nh-finescale/ln2block/documentation/img/Kranenburg.jpg

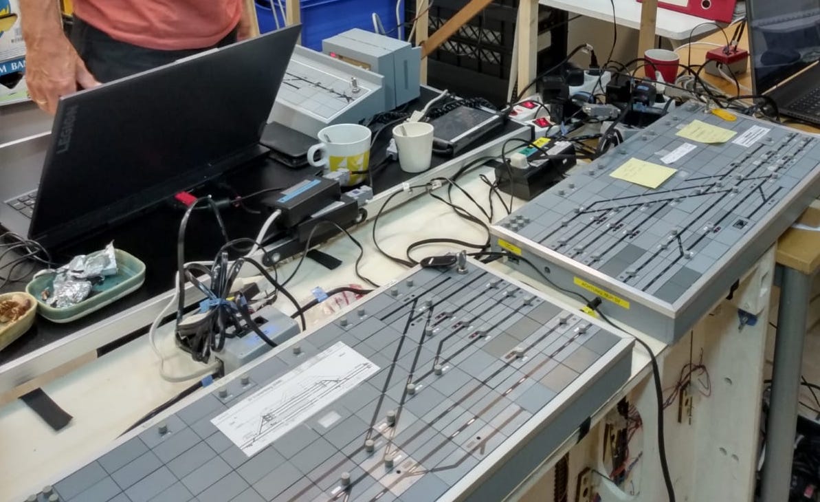
documentation/img/Kranenburg.jpg
