nh-finescale/ln2block/documentation/img/ln2b-statusdisplay.jpg

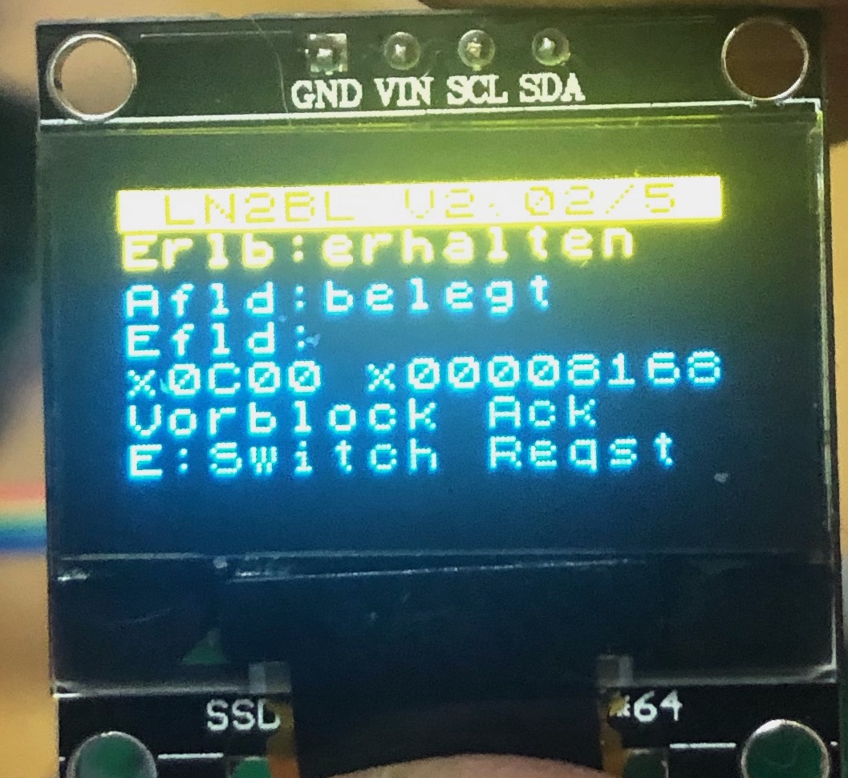
documentation/img/ln2b-statusdisplay.jpg
