nh-finescale/ln2block/documentation/img/ln2bv5-conn.png

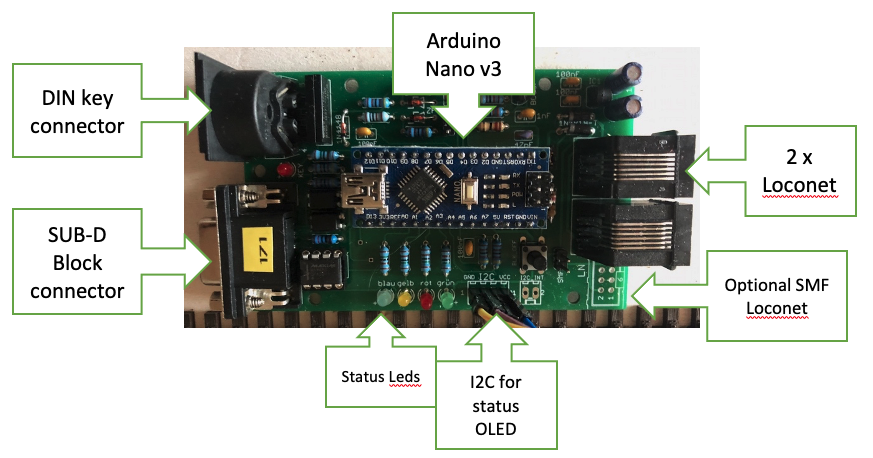
documentation/img/ln2bv5-conn.png
