nh-finescale/ln2block/documentation/img/ln2bv6s.jpg

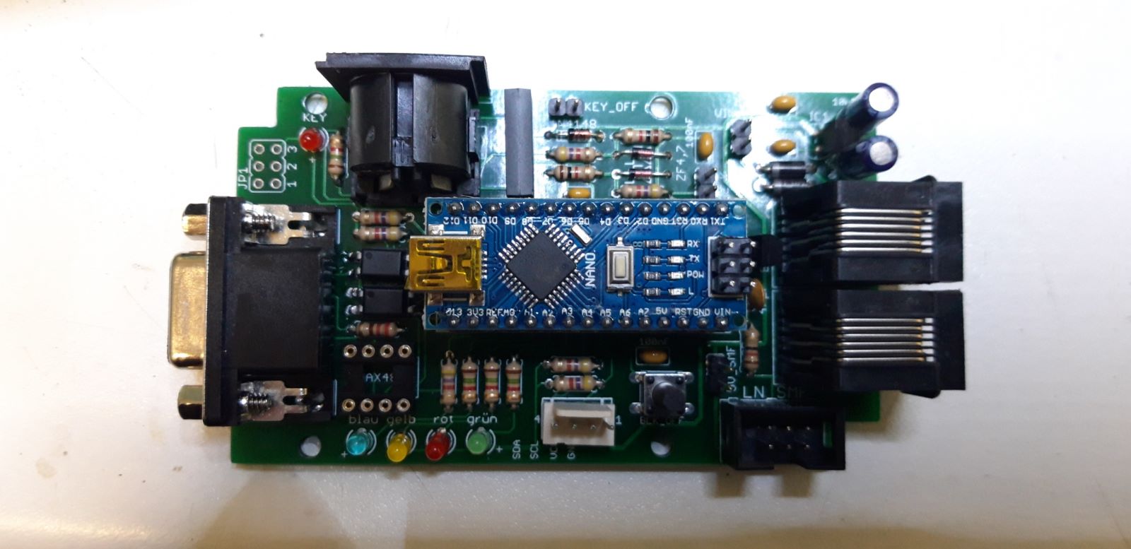
documentation/img/ln2bv6s.jpg
