nh-finescale/ln2block/documentation/img/LN2Block_Build_22.jpg

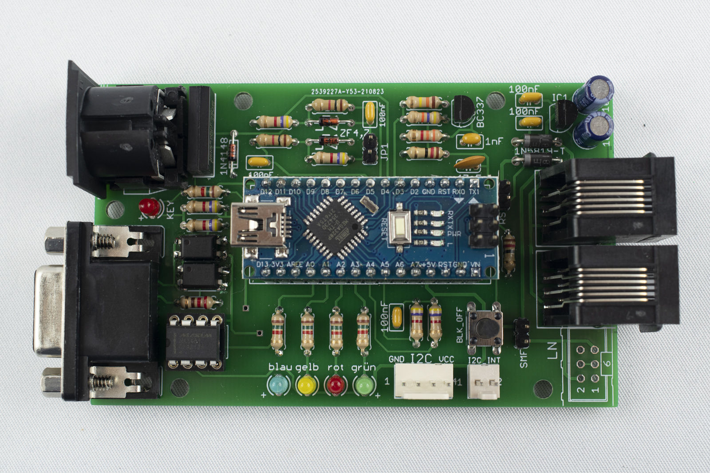
documentation/img/LN2Block_Build_22.jpg
