nh-finescale/ln2block/src/Loconet2Block/my_loconet.cpp

//##########################################################################
//#
//#		MyLoconetClass
//#
//#	Diese Klasse behandelt alle Loconet-Nachrichten und was damit
//#	zusammen hängt.
//#
//#-------------------------------------------------------------------------
//#
//#	File Version:	33		from: 30.05.2026
//#
//#	Implementation:
//#		-	add second track contact
//#			new function
//#				SendContactAusfahrtOccupied()
//#
//#-------------------------------------------------------------------------
//#
//#	File Version:	32		from: 01.01.2026
//#
//#	Implementation:
//#		-	add handling for a distant signal
//#			change in function
//#				LoconetReceived()
//#
//#-------------------------------------------------------------------------
//#
//#	File Version:	31		from: 21.08.2024
//#
//#	Implementation:
//#		-	improvement of notify messages
//#			don't react on notifySwitchReport and notifySwitchState
//#			to avoid missinterpretation of requests.
//#			delete functions
//#				notifySwitchReport()
//#				notifySwitchState()
//#
//#-------------------------------------------------------------------------
//#
//#	File version:	30		from: 12.11.2023
//#
//#	Implementation:
//#		-	switch to LocoNet Library V1.1.13
//#			change in function
//#				notifyLNCVread()
//#
//#-------------------------------------------------------------------------
//#
//#	File version:	29		from: 09.08.2023
//#
//#	Implementation:
//#		-	change handling of ESTGWJ mode
//#			new variable
//#				m_bIsEstwgjMode
//#			change in function
//#				Init()
//#				LoconetReceived()
//#
//#-------------------------------------------------------------------------
//#
//#	File version:	28		from: 07.08.2023
//#
//#	Bug Fix:
//#		-	problem after change of module address fixed
//#			change in function
//#				notifyLNCVwrite()
//#
//#-------------------------------------------------------------------------
//#
//#	File version:	27		from: 26.07.2023
//#
//#	Bug Fix:
//#		-	by mistake no acknowledge was send when receiving a programming
//#			start with broadcast as address.
//#
//#-------------------------------------------------------------------------
//#
//#	File version:	26		from: 18.07.2023
//#
//#	Bug Fix:
//#		-	do not go into prog mode when a programming start msg
//#			with broadcast address was detected
//#			change in function
//#				notifyLNCVprogrammingStart()
//#
//#-------------------------------------------------------------------------
//#
//#	File version:	25		from: 04.06.2023
//#
//#	Bug Fix:
//#		-	do not go into prog mode when a discover msg was detected
//#			change in function
//#				notifyLNCVdiscover()
//#
//#-------------------------------------------------------------------------
//#
//#	File version:	24		from: 16.05.2023
//#
//#	Implementation:
//#		-	new definitions for train number field types
//#				TRAIN_NUMBER_FIELD_ALL
//#			this type is used to address all ZN fields with one message
//#			changes in function
//#				CheckForMessageAndStoreInDataPool()
//#				SendBlock2Station()
//#
//#-------------------------------------------------------------------------
//#
//#	File version:	23		from: 07.04.2023
//#
//#	Bug Fix:
//#		-	ignore the second switch message with output set to '0'
//#			changes in functions
//#				LoconetReceived()
//#				notifySwitchRequest()
//#				notifySwitchReport()
//#				notifySwitchState()
//#
//#-------------------------------------------------------------------------
//#
//#	File version:	22		from: 07.02.2023
//#
//#	Bug Fix:
//#		-	wrong messages were send, so move the print out calls
//#			change in functions
//#				LoconetReceived()
//#				SendBlockMessage()
//#
//#-------------------------------------------------------------------------
//#
//#	File version:	21		from: 01.02.2023
//#
//#	Bug Fix:
//#		-	wrong message send by 'Rückblock'
//#
//#	Implementation:
//#		-	change train number field codes to new definitions
//#
//#-------------------------------------------------------------------------
//#
//#	File version:	20		from: 31.01.2023
//#
//#	Implementation:
//#		-	add ESTWGJ mode
//#			new function
//#				SendBlockMessage()
//#
//#-------------------------------------------------------------------------
//#
//#	File version:	19		from: 04.01.2023
//#
//#	Bug Fix:
//#		-	don't react on Loconet messages when Block is OFF
//#			new variable
//#				m_bBlockOn
//#
//#-------------------------------------------------------------------------
//#
//#	File version:	18		from: 15.12.2022
//#
//#	Bug Fix:
//#		-	handle the correct sturcture pointer to
//#			function getTrainNumber()
//#		-	forget to set usDigit in function DecodeTrainNumberDigit()
//#
//#-------------------------------------------------------------------------
//#
//#	File version:	17		from: 14.11.2022
//#
//#	Implementation:
//#		-	change loconet message handling
//#
//#-------------------------------------------------------------------------
//#
//#	File version:	16		from: 01.11.2022
//#
//#	Implementation:
//#		-	add message to switch the box OFF / ON
//#			changes in function 'LoconetReceived()'
//#
//#-------------------------------------------------------------------------
//#
//#	File version:	15		from: 02.10.2022
//#
//#	Implementation:
//#		-	add version number into EEPROM
//#			changes in function 'notifyLNCVwrite()'
//#		-	store article number and module address in global variables
//#			to simple access and speed up LNCV read and write
//#
//#-------------------------------------------------------------------------
//#
//#	File version:	14		from: 11.09.2022
//#
//#	Implementation:
//#		-	add new functions
//#				SendContactOccupied()	state of internal contact
//#				SendBlockOn()			state of block (ON / OFF)
//#		-	remove Function SendMessageWithInAdr() because it is
//#			not used anymore
//#
//#-------------------------------------------------------------------------
//#
//#	File version:	13		from: 09.09.2022
//#
//#	Implementation:
//#		-	the flag for train numbers moved to 'lncv_storage',
//#			because it will be stored permanent now.
//#
//#-------------------------------------------------------------------------
//#
//#	File version:	12		from: 28.08.2022
//#
//#	Implementation:
//#		-	add send the states of all OUT-Loconet-Devices
//#			changes in function
//#				LoconetReceived()
//#
//#-------------------------------------------------------------------------
//#
//#	File version:	11		from: 09.07.2022
//#
//#	Implementation:
//#		-	add reset functionality over loconet
//#			changes in functions
//#				CheckForMessageAndStoreInDataPool()
//#				LoconetReceived()
//#			add new variable m_bDoReset
//#
//#-------------------------------------------------------------------------
//#
//#	File version:	10		from: 04.03.2022
//#
//#	Bug Fix:
//#		-	correction of parameter usage for switching train number
//#			messages on / off
//#			 -	function LoconetReceived()
//#		-	avoid evaluation of per loop-back received train number message
//#			 -	new member variable 'm_bIgnoreMsg'
//#			 -	function Init()
//#			 -	function SendBlock2Station()
//#			 -	function CheckForMessageAndStoreInDataPool()
//#
//#-------------------------------------------------------------------------
//#
//#	File version:	9		from: 04.03.2022
//#
//#	Implementation:
//#		-	put indicator into ZN message which ZN field to address
//#		-	add flag that shows if handling of train number messages
//#			is enabled
//#
//#-------------------------------------------------------------------------
//#
//#	File version:	8		from: 26.02.2022
//#
//#	Implementation:
//#		-	add address for annunciator field use for train numbers
//#
//#-------------------------------------------------------------------------
//#
//#	File version:	7		from: 25.02.2022
//#
//#	Implementation:
//#		-	add new message handling for FREMO train numbers
//#
//#-------------------------------------------------------------------------
//#
//#	File version:	6		from: 15.01.2022
//#
//#	Bug Fix:
//#		-	In der Funktion 'notifyLNCVwrite()' wurde versehentlich der
//#			falsche Parameter an die Funktion 'PrintLncvReadWrite()'
//#			übergeben, so das der Text 'Read' ausgegeben wurde.
//#			Dies wurde korrigiert und es wird der Text 'Write' ausgegeben.
//#		-	In der Funktion 'notifyLNCVprogrammingStart()' wurde die
//#			Debugging-Ausgabe an das Ende der Funktion verschoben.
//#			Dadurch wird die Box-Adresse ausgegeben, wenn eine Broadcast-
//#			Nachricht benutzt wurde, um in den Programmiermodus zu wechseln.
//#
//#-------------------------------------------------------------------------
//#
//#	File version:	5		from: 29.12.2021
//#
//#	Implementation:
//#		-	Durch den Einbau von "Block On / Off" wurde die Initialisierung
//#			geändert. Dafür wurde die Funktion Init() angepasst,
//#			die Funktion StartLoconet2Block() gelöscht und die Funktion
//#			AskForSignalState() neu erstellt.
//#		-	Wenn der Programmiermodus beendet wird, wird nun ein RESET
//#			ausgelöst.
//#
//#-------------------------------------------------------------------------
//#
//#	File version:	4		from: 01.12.2021
//#
//#	Implementation:
//#		-	In der Funktion SendMessageWithInAdr() die Information
//#			nicht invertiert, wenn der interne Kontakt benutzt wird und
//#			es sich um eine Einfahr-Kontakt-Nachricht handelt.
//#
//#-------------------------------------------------------------------------
//#
//#	File version:	3		from: 12.11.2021
//#
//#	Implementation:
//#		-	Das Display kann nun um 180 Grad gedreht werden.
//#			Gesteuert wird dies durch das Konfigurationsbit 'DISPLAY_FLIP'.
//#			Ist das Bit gesetzt, wird das Display um 180 Grad gedreht.
//#			Funktion:	StartLoconet2Block()
//#
//#-------------------------------------------------------------------------
//#
//#	File version:	2		from: 28.10.2021
//#
//#	Implementation:
//#		-	Zwischen zwei zu sendenden Loconet-Nachrichten wird nun
//#			eine konfigurierbare Wartezeit gewartet.
//#			Funktionen:	SendMessageWithInAdr()
//#						SendMessageWithOutAdr()
//#
//#-------------------------------------------------------------------------
//#
//#	File version:	1		from: 14.09.2021
//#
//#	Implementation:
//#		-	first working version
//#
//##########################################################################


//==========================================================================
//
//		I N C L U D E S
//
//==========================================================================

#include "compile_options.h"

#include <Arduino.h>
#include <LocoNet.h>


#ifdef DEBUGGING_PRINTOUT
#include "debugging.h"
#endif

#include "my_loconet.h"
#include "data_pool.h"
#include "lncv_storage.h"
#include "signal_aspect_codes.h"



//==========================================================================
//
//		D E F I N I T I O N S
//
//==========================================================================

#if PLATINE_VERSION == 4
	#define LOCONET_TX_PIN			4
#else
	#define LOCONET_TX_PIN			7
#endif

#define	DIR_RED			0
#define DIR_THROWN		0
#define DIR_GREEN		1
#define DIR_CLOSED		1


//==========================================================================
//
//		G L O B A L   V A R I A B L E S
//
//==========================================================================

MyLoconetClass	 g_clMyLoconet		= MyLoconetClass();

LocoNetCVClass	 g_clLNCV;
lnMsg			*g_pLnPacket;

uint16_t	g_uiArticleNumber;
uint16_t	g_uiModuleAddress;


#ifdef DEBUGGING_PRINTOUT

char		g_chTrainNumber[] = "L 123456";


//==========================================================================
//
//		G L O B A L   F U N C T I O N S
//
//==========================================================================

//*****************************************************************
//	DecodeTrainNumberDigit
//
uint8_t DecodeTrainNumberDigit( uint8_t usValue )
{
	uint8_t		usDigit;
	bool		bFlash		= (0 != (0x10 & usValue));

	switch( usValue )
	{
		case ' ':
		case 'L':
		case 'B':
			usDigit = usValue;
			break;

		case 0x1E:
			bFlash = true;

		case 0x0E:
			usDigit = 'F';
			break;

		case 0x0F:
		case 0x1F:
			usDigit = ' ';
			break;

		default:
			bFlash   = (0 != (0x10 & usValue));
			usValue &= 0x0F;
			usDigit  = '0' + usValue;
			break;
	}
	
	if( bFlash )
	{
		usDigit |= 0x80;
	}
	
	return( usDigit );
}


//*****************************************************************
//	getTrainNumber
//
void getTrainNumber( uint8_t chDir, peerXferMsg *pMsg )
{
	g_chTrainNumber[ 0 ] = chDir;
	g_chTrainNumber[ 1 ] = ' ';
	g_chTrainNumber[ 2 ] = DecodeTrainNumberDigit( pMsg->d1 );
	g_chTrainNumber[ 3 ] = DecodeTrainNumberDigit( pMsg->d2 );
	g_chTrainNumber[ 4 ] = DecodeTrainNumberDigit( pMsg->d3 );
	g_chTrainNumber[ 5 ] = DecodeTrainNumberDigit( pMsg->d4 );
	g_chTrainNumber[ 6 ] = DecodeTrainNumberDigit( pMsg->d5 );
	g_chTrainNumber[ 7 ] = DecodeTrainNumberDigit( pMsg->d6 );
}

#endif


//==========================================================================
//
//		C L A S S   F U N C T I O N S
//
//==========================================================================


///////////////////////////////////////////////////////////////////////
//	CLASS: MyLoconetClass
//

//*****************************************************************
//	Constructor
//
MyLoconetClass::MyLoconetClass()
{
}


//*****************************************************************
//	Init
//
void MyLoconetClass::Init( void )
{
	m_bBlockOn			= true;
	m_bIgnoreMsg		= false;
	m_bDoReset			= false;

	g_uiArticleNumber	= g_clLncvStorage.ReadLNCV( LNCV_ADR_ARTIKEL_NUMMER );
	g_uiModuleAddress	= g_clLncvStorage.ReadLNCV( LNCV_ADR_MODULE_ADDRESS );

	m_bIsEstwgjMode		= g_clLncvStorage.IsConfigSet( ESTWGJ_MODE );

	LocoNet.init( LOCONET_TX_PIN );
}


//*****************************************************************
//	StartLoconet2Block
//
void MyLoconetClass::AskForSignalState( void )
{
	if( 0 < g_clLncvStorage.GetInAddress( IN_IDX_EINFAHR_SIGNAL ) )
	{
		LocoNet.reportSwitch( g_clLncvStorage.GetInAddress( IN_IDX_EINFAHR_SIGNAL ) );
	}

	if( 0 < g_clLncvStorage.GetInAddress( IN_IDX_AUSFAHR_SIGNAL ) )
	{
		LocoNet.reportSwitch( g_clLncvStorage.GetInAddress( IN_IDX_AUSFAHR_SIGNAL ) );
	}
}


//*****************************************************************
//	CheckForAndHandleMessage
//
bool MyLoconetClass::CheckForMessageAndStoreInDataPool( void )
{
	uint16_t	uiAddress = 0;
	

	g_pLnPacket = LocoNet.receive();

	while( g_pLnPacket )
	{
		if( m_bIgnoreMsg )
		{
			m_bIgnoreMsg = false;
		}
		else if( !LocoNet.processSwitchSensorMessage( g_pLnPacket ) )
		{
			if( !g_clLNCV.processLNCVMessage( g_pLnPacket ) )
			{
				if( 	(OPC_PEER_XFER == g_pLnPacket->px.command)
					&&	(16 == g_pLnPacket->px.mesg_size)			)
				{
					//----------------------------------------------
					//	this is a FREMO train number message
					//	so send it over the block cable
					//
					if(		g_clLncvStorage.IsTrainNumbersOn()
						&&	g_clLncvStorage.IsConfigSet( TRAIN_NUMBERS ) )
					{
						uiAddress  =  g_pLnPacket->px.dst_h << 7;
						uiAddress |= (g_pLnPacket->px.dst_l & 0x7F);

						g_pLnPacket->px.dst_h = 0;

						//------------------------------------------
						//	now tell the other end of the block
						//	cable which ZN field to address
						//
						if( 0x0000 == uiAddress )
						{
							g_pLnPacket->px.dst_l = TRAIN_NUMBER_FIELD_ALL;

							g_clDataPool.ReceiveTrainNoFromStation( (uint8_t *)g_pLnPacket );
#ifdef DEBUGGING_PRINTOUT
							getTrainNumber( 'L', (peerXferMsg *)g_pLnPacket );
							g_clDebugging.PrintTrainNumber( ZN_ALL, g_chTrainNumber );
#endif
						}
						else if( g_clLncvStorage.GetTrainNoAddressTrack() == uiAddress )
						{
							g_pLnPacket->px.dst_l = TRAIN_NUMBER_FIELD_TRACK;

							g_clDataPool.ReceiveTrainNoFromStation( (uint8_t *)g_pLnPacket );
#ifdef DEBUGGING_PRINTOUT
							getTrainNumber( 'L', (peerXferMsg *)g_pLnPacket );
							g_clDebugging.PrintTrainNumber( ZN_TRACK, g_chTrainNumber );
#endif
						}
						else if( g_clLncvStorage.GetTrainNoAddressOffer() == uiAddress )
						{
							g_pLnPacket->px.dst_l = TRAIN_NUMBER_FIELD_OFFER;

							g_clDataPool.ReceiveTrainNoFromStation( (uint8_t *)g_pLnPacket );
#ifdef DEBUGGING_PRINTOUT
							getTrainNumber( 'L', (peerXferMsg *)g_pLnPacket );
							g_clDebugging.PrintTrainNumber( ZN_OFFER, g_chTrainNumber );
#endif
						}
						else if( g_clLncvStorage.GetTrainNoAddressAnnunciatorRemote() == uiAddress )
						{
							g_pLnPacket->px.dst_l = TRAIN_NUMBER_FIELD_ANNUNCIATOR;

							g_clDataPool.ReceiveTrainNoFromStation( (uint8_t *)g_pLnPacket );
#ifdef DEBUGGING_PRINTOUT
							getTrainNumber( 'L', (peerXferMsg *)g_pLnPacket );
							g_clDebugging.PrintTrainNumber( ZN_ANNUNCIATOR, g_chTrainNumber );
#endif
						}
					}
				}
			}
		}

		if( m_bDoReset )
		{
			g_pLnPacket = NULL;
		}
		else
		{
			g_pLnPacket = LocoNet.receive();
		}
	}

	return( m_bDoReset );
}


//*****************************************************************
//	SendBlockMessage
//
void MyLoconetClass::SendBlockMessage(	uint16_t	uiAsSensor,
										uint16_t	uiIsInvert,
										bool		bIsSensor,
										uint8_t		usDir,
										uint8_t		usAdrIdx,
										uint8_t		usBlockMsg	)
{
	uint16_t	uiMask = 0x0001 << usAdrIdx;

	//--------------------------------------------------------
	//	first check if we are searching for a sensor message
	//	or a switch message.
	//
	//	bIsSensor == false	we are looking for switch messages
	//	bIsSensor == true	we are looking for sensor messages
	//
	//	uiAsSensor will hold the info if the message at the
	//	actual bit position (uiMask) is expected to be
	//	a sensor message or a switch message.
	//	(bit set => sensor message)
	//
	if( bIsSensor == (0 != (uiAsSensor & uiMask)) )
	{
		//------------------------------------------------
		//	Check if direction should be inverted
		//
		if( uiIsInvert & uiMask )
		{
			if( 0 == usDir )
			{
				usDir = 1;
			}
			else
			{
				usDir = 0;
			}
		}

		//------------------------------------------------
		//	only send the message when we get a 'GREEN'
		//	direction
		//
		if( 0 != usDir )
		{
			g_clDataPool.SetSendBlockMessage( 1 << usBlockMsg );

#ifdef DEBUGGING_PRINTOUT
			if( IN_IDX_BEDIENUNG_HILFSVORBLOCK == usAdrIdx )
			{
				g_clDebugging.PrintAnfangsfeldState( ANFANGSFELD_STATE_BELEGT );
			}
			else if( IN_IDX_BEDIENUNG_RUECKBLOCK == usAdrIdx )
			{
				g_clDebugging.PrintEndfeldState( ENDFELD_STATE_FREI );
			}
			else if( IN_IDX_BEDIENUNG_ERLAUBNISABGABE == usAdrIdx )
			{
				g_clDebugging.PrintErlaubnisState( ERLAUBNIS_STATE_ABGEGEBEN );
			}
#endif
		}
	}
}


//*****************************************************************
//	SendBlock2Station
//
void MyLoconetClass::SendBlock2Station( uint8_t *pMsg )
{
	lnMsg		*pHelper	= (lnMsg *)pMsg;
	uint16_t	 uiAddress	= 0;

	if( TRAIN_NUMBER_FIELD_ALL == pHelper->px.dst_l )
	{
		uiAddress = 0x0000;

#ifdef DEBUGGING_PRINTOUT
		getTrainNumber( 'B', (peerXferMsg *)pHelper );
		g_clDebugging.PrintTrainNumber( ZN_ALL, g_chTrainNumber );
#endif
	}
	else if( TRAIN_NUMBER_FIELD_ANNUNCIATOR == pHelper->px.dst_l )
	{
		uiAddress = g_clLncvStorage.GetTrainNoAddressAnnunciatorLocal();

#ifdef DEBUGGING_PRINTOUT
		getTrainNumber( 'B', (peerXferMsg *)pHelper );
		g_clDebugging.PrintTrainNumber( ZN_ANNUNCIATOR, g_chTrainNumber );
#endif
	}
	else if( TRAIN_NUMBER_FIELD_OFFER == pHelper->px.dst_l )
	{
		uiAddress = g_clLncvStorage.GetTrainNoAddressOffer();

#ifdef DEBUGGING_PRINTOUT
		getTrainNumber( 'B', (peerXferMsg *)pHelper );
		g_clDebugging.PrintTrainNumber( ZN_OFFER, g_chTrainNumber );
#endif
	}
	else if( TRAIN_NUMBER_FIELD_TRACK == pHelper->px.dst_l )
	{
		uiAddress = g_clLncvStorage.GetTrainNoAddressTrack();

#ifdef DEBUGGING_PRINTOUT
		getTrainNumber( 'B', (peerXferMsg *)pHelper );
		g_clDebugging.PrintTrainNumber( ZN_TRACK, g_chTrainNumber );
#endif
	}

	pHelper->px.dst_h = (uint8_t)((uiAddress >> 7) & 0x7F);
	pHelper->px.dst_l = (uint8_t)( uiAddress & 0x7F);

	//----------------------------------------------------------
	//	send out a train number message
	//	set flag to avoid evaluation of this msg by myself,
	//	because internal loop-back of loconet messages.
	//
	m_bIgnoreMsg = true;
	
	if( LN_DONE != LocoNet.send( pHelper ) )
	{
		m_bIgnoreMsg = false;
	}
}


//******************************************************************
//	SendContactOccupied
//------------------------------------------------------------------
//	This function sends a loconet message with the state of the
//	internal contact.
//	If the contact is occupied it sends a 'red' and
//	if the contact is free it sends a 'green'.
//
void MyLoconetClass::SendContactOccupied( bool bOccupied )
{
	uint16_t	config		= g_clLncvStorage.GetConfigReceive();
	uint16_t	inverted	= g_clLncvStorage.GetInvertReceive();
	uint16_t	adr			= g_clLncvStorage.GetInAddress( IN_IDX_EINFAHR_KONTAKT );
	uint8_t		dir			= DIR_GREEN;
	bool		bDoInvert	= false;
	bool		bIsSensor	= false;


	//---------------------------------------------------------
	//	send the message only if there is an address for it
	//
	if( 0 < adr )
	{
		if( bOccupied )
		{
			dir = DIR_RED;
		}

		//-----------------------------------------------------
		//	Check if 'dir' should be inverted
		//
		if( inverted & IN_MASK_EINFAHR_KONTAKT )
		{
			bDoInvert = true;
		}

		//-----------------------------------------------------
		//	Check if this should be a sensor
		//	or a switch message
		//
		if( config & IN_MASK_EINFAHR_KONTAKT )
		{
			bIsSensor = true;
		}

		SendMessage( adr, dir, bDoInvert, bIsSensor );
	}
}


#if PLATINE_VERSION == 7

//******************************************************************
//	SendContactAusfahrtOccupied
//------------------------------------------------------------------
//	This function sends a loconet message with the state of the
//	internal contact.
//	If the contact is occupied it sends a 'red' and
//	if the contact is free it sends a 'green'.
//
void MyLoconetClass::SendContactAusfahrtOccupied( bool bOccupied )
{
	uint16_t	config		= g_clLncvStorage.GetConfigReceive();
	uint16_t	inverted	= g_clLncvStorage.GetInvertReceive();
	uint16_t	mask		= (uint16_t)1;
	uint16_t	adr			= g_clLncvStorage.GetInAddress( IN_IDX_AUSFAHR_KONTAKT );
	uint8_t		dir			= DIR_GREEN;
	bool		bDoInvert	= false;
	bool		bIsSensor	= false;


	//---------------------------------------------------------
	//	send the message only if there is an address for it
	//
	if( 0 < adr )
	{
		if( bOccupied )
		{
			dir = DIR_RED;
		}

		//-----------------------------------------------------
		//	Check if 'dir' should be inverted
		//
		if( inverted & IN_MASK_AUSFAHR_KONTAKT )
		{
			bDoInvert = true;
		}

		//-----------------------------------------------------
		//	Check if this should be a sensor
		//	or a switch message
		//
		if( config & IN_MASK_AUSFAHR_KONTAKT )
		{
			bIsSensor = true;
		}

		SendMessage( adr, dir, bDoInvert, bIsSensor );
	}
}

#endif


//******************************************************************
//	SendBlockOn
//------------------------------------------------------------------
//	This function sends a loconet message with the state of the
//	block (ON / OFF)
//	If the block is ON it sends a 'green' and
//	if the block is OFF it sends a 'red'
//
void MyLoconetClass::SendBlockOn( bool bBlockOn )
{
	uint16_t	adr	= g_clLncvStorage.GetBlockOnOffAddress();
	uint8_t		dir	= DIR_RED;


	if( bBlockOn )
	{
		dir = DIR_GREEN;
	}

	//----	switch message  ---------------------------
	//
	LocoNet.requestSwitch( adr, 1, dir );

#ifdef DEBUGGING_PRINTOUT
	g_clDebugging.PrintReportSwitchMsg( adr, dir );
#endif

	//----	wait befor sending the next message  ------
	//
	delay( 10 + g_clLncvStorage.GetSendDelayTime() );

	LocoNet.requestSwitch( adr, 0, dir );


	//----	wait befor sending the next message  ---------------
	//
	delay( g_clLncvStorage.GetSendDelayTime() );
}


//******************************************************************
//	LoconetReceived
//------------------------------------------------------------------
//	This function checks if the received message is for 'us'.
//	This is done by checking whether the address of the message
//	matches one of the stored addresses.
//	If so, the corresponding bit of the 'InState' will be set
//	according to the info in the message.
//
void MyLoconetClass::LoconetReceived( bool isSensor, uint16_t adr, uint8_t dir )
{
	uint16_t	configRecv	= g_clLncvStorage.GetConfigReceive();
	uint16_t	inverted	= g_clLncvStorage.GetInvertReceive();
	uint16_t	mask		= 0x0001;


	//--------------------------------------------------------------
	//	Handle special messages like RESET
	//	the special messages must be of type 'switch'
	//
	if( !isSensor )
	{
		if( g_clLncvStorage.GetTrainNoAddressEnable() == adr )
		{
			//------------------------------------------------------
			//	this is the message to enable/disable handling of
			//	train number messages
			//
			if( DIR_RED == dir )
			{
				g_clLncvStorage.SetTrainNumbersOn( false );
			}
			else
			{
				g_clLncvStorage.SetTrainNumbersOn( true );
			}

			return;
		}

		//----------------------------------------------------------
		//	switch display between showing
		//		-	Loconet and block messages
		//		-	train numbers
		//
#ifdef DEBUGGING_PRINTOUT
		if( g_clLncvStorage.GetShowTrainNumbersAddress() == adr )
		{
			if( DIR_RED == dir )
			{
				g_clLncvStorage.SetShowTrainNumbers( false );
				g_clDebugging.PrintInfoLine( infoLineMessages );
			}
			else
			{
				g_clLncvStorage.SetShowTrainNumbers( true );
				g_clDebugging.PrintInfoLine( infoLineTrainNumbers );
			}
		}
#endif

		//----------------------------------------------------------
		//	send state for all OUT-Loconet-Devices
		//
		if( g_clLncvStorage.GetSendDeviceStateAddress() == adr )
		{
			g_clDataPool.SendOutState();

			return;
		}

		if( g_clLncvStorage.GetBlockOnOffAddress() == adr )
		{
			//------------------------------------------------------
			//	this is the message to switch the block on or off
			//
			if( DIR_RED == dir )
			{
				if( g_clLncvStorage.IsBlockOn() )
				{
					g_clLncvStorage.SetBlockOn( false );
					g_clDataPool.SwitchBlockOff();
					m_bBlockOn = false;
				}
			}
			else
			{
				g_clLncvStorage.SetBlockOn( true );
				m_bDoReset = true;
			}

			return;
		}

		if( g_clLncvStorage.GetResetAddress() == adr )
		{
			//------------------------------------------------------
			//	this is the message to do a reset of the box
			//
			m_bDoReset = true;

			return;
		}
	}

	//--------------------------------------------------------------
	//	if the block is switched OFF then stop processing here
	//
	if( !m_bBlockOn )
	{
		return;
	}

	//--------------------------------------------------------------
	//	ESTWGJ Mode
	//
	if( m_bIsEstwgjMode )
	{
		if( g_clLncvStorage.GetInAddress( IN_IDX_BEDIENUNG_RUECKBLOCK ) == adr )
		{
			SendBlockMessage(	configRecv, inverted, isSensor, dir,
								IN_IDX_BEDIENUNG_RUECKBLOCK,
								DP_BLOCK_MESSAGE_RUECKBLOCK			);
		}

		if( g_clLncvStorage.GetInAddress( IN_IDX_BEDIENUNG_HILFSVORBLOCK ) == adr )
		{
			SendBlockMessage(	configRecv, inverted, isSensor, dir,
								IN_IDX_BEDIENUNG_HILFSVORBLOCK,
								DP_BLOCK_MESSAGE_VORBLOCK			);
		}

		if( g_clLncvStorage.GetInAddress( IN_IDX_BEDIENUNG_ERLAUBNISABGABE ) == adr )
		{
			SendBlockMessage(	configRecv, inverted, isSensor, dir,
								IN_IDX_BEDIENUNG_ERLAUBNISABGABE,
								DP_BLOCK_MESSAGE_ERLAUBNIS_ABGABE	);
		}

		return;
	}

	//--------------------------------------------------------------
	//	block is ON, so process Loconet messages
	//
	for( uint8_t idx = 0 ; LOCONET_IN_COUNT > idx ; idx++ )
	{
		//--------------------------------------------------------
		//	first check if we are searching for an address in
		//	a sensor message or in a switch message.
		//
		//	isSensor == false	we are looking for switch messages
		//	isSensor == true	we are looking for sensor messages
		//
		//	configRecv will hold the info if the message at the
		//	actual bit position (mask) is expected to be
		//	a sensor message or a switch message.
		//	(bit set => sensor message)
		//
		if( isSensor == (0 != (configRecv & mask)) )
		{
			if(		(0 < g_clLncvStorage.GetInAddress( idx ))
				&&	(adr == g_clLncvStorage.GetInAddress( idx )) )
			{
				//------------------------------------------------
				//	This is one of our addresses, ergo go on
				//	with the processing...
				//

#ifdef DEBUGGING_PRINTOUT
				g_clDebugging.PrintNotifyMsg( idx, adr, dir, 0 );
#endif

				//------------------------------------------------
				//	Check if 'dir' should be inverted
				//
				if( inverted & mask )
				{
					if( 0 == dir )
					{
						dir = 1;
					}
					else
					{
						dir = 0;
					}
				}

				//------------------------------------------------
				//	always set the 'InState' if the message comes
				//	from a push button device.
				//	otherwise set the 'InState' according to
				//	the 'dir' parameter of the message
				//
//				if(		(0 != dir)
//					||	(	(IN_IDX_BEDIENUNG_RUECKBLOCK	 <= idx)
//						&&	(IN_IDX_BEDIENUNG_ANSCHALTER_AUS >= idx)) )
				if( 0 != dir )
				{
					g_clDataPool.SetInState( mask );
				}
				else
				{
					g_clDataPool.ClearInState( mask );
				}

				//------------------------------------------------
				//	store signal messages for 'Prüfschleife'
				//	and for an 'Einfahr-Signal' send the state
				//	over the block line to the next station
				//
				if( IN_IDX_EINFAHR_SIGNAL == idx )
				{
					g_clDataPool.SetInState( ((uint16_t)1 << DP_E_SIG_SEND) );

					if( 0 != dir )
					{
						g_clDataPool.SetDistantSignalAspect( SIGNAL_ASPECT_CODE__GO );
					}
					else
					{
						g_clDataPool.SetDistantSignalAspect( SIGNAL_ASPECT_CODE__STOP );
					}
				}
	
				if( IN_IDX_AUSFAHR_SIGNAL == idx )
				{
					g_clDataPool.SetInState( ((uint16_t)1 << DP_A_SIG_SEND) );
				}
			}
		}

		mask <<= 1;
	}
}


//*****************************************************************
//	SendMessage
//
void MyLoconetClass::SendMessage(	uint16_t	adr,
									uint8_t		dir,
									bool		bDoInvert,
									bool		bIsSensor	)
{
	//----------------------------------------------------------
	//	Check if 'dir' should be inverted
	//
	if( bDoInvert )
	{
		if( 0 < dir )
		{
			dir = 0;
		}
		else
		{
			dir = 1;
		}
	}

	//----------------------------------------------------------
	//	Check if this should be a sensor
	//	or a switch message
	//
	if( bIsSensor )
	{
		//----	sensor message  ----------------------------
		//
		LocoNet.reportSensor( adr, dir );

#ifdef DEBUGGING_PRINTOUT
		g_clDebugging.PrintReportSensorMsg( adr, dir );
#endif
	}
	else
	{
		//----	switch message  ----------------------------
		//
		LocoNet.requestSwitch( adr, 1, dir );

#ifdef DEBUGGING_PRINTOUT
		g_clDebugging.PrintReportSwitchMsg( adr, dir );
#endif

		//----	wait befor sending the next message  -------
		//
		delay( g_clLncvStorage.GetSendDelayTime() );

		LocoNet.requestSwitch( adr, 0, dir );
	}

	//----	wait befor sending the next message  -----------
	//
	delay( g_clLncvStorage.GetSendDelayTime() );
}


//*****************************************************************
//	SendMessageWithOutAdr
//
void MyLoconetClass::SendMessageWithOutAdr( uint8_t idx, uint8_t dir )
{
	uint32_t	configSend	= g_clLncvStorage.GetConfigSend();
	uint32_t	inverted	= g_clLncvStorage.GetInvertSend();
	uint32_t	mask		= (uint32_t)1;
	uint16_t	adr			= g_clLncvStorage.GetOutAddress( idx );
	bool		bDoInvert	= false;
	bool		bIsSensor	= false;

	//---------------------------------------------------------
	//	send the message only if there is an address for it
	//
	if( 0 < adr )
	{
		mask <<= idx;

		//-----------------------------------------------------
		//	Check if 'dir' should be inverted
		//
		if( inverted & mask )
		{
			bDoInvert = true;
		}

		//-----------------------------------------------------
		//	Check if this should be a sensor
		//	or a switch message
		//
		if( configSend & mask )
		{
			bIsSensor = true;
		}

		SendMessage( adr, dir, bDoInvert, bIsSensor );
	}
}


//==========================================================================
//
//		L O C O N E T   C A L L B A C K   F U N C T I O N S
//
//==========================================================================


//**********************************************************************
//
void notifySensor( uint16_t Address, uint8_t State )
{
#ifdef DEBUGGING_PRINTOUT
	g_clDebugging.PrintNotifyType( NT_Sensor );
#endif

	g_clMyLoconet.LoconetReceived( true, Address, State );
}


//**********************************************************************
//
void notifySwitchRequest( uint16_t Address, uint8_t Output, uint8_t Direction )
{
#ifdef DEBUGGING_PRINTOUT
	g_clDebugging.PrintNotifyType( NT_Request );
#endif

	if( Output )
	{
		g_clMyLoconet.LoconetReceived( false, Address, Direction );
	}
}



//**********************************************************************
//
int8_t notifyLNCVdiscover( uint16_t &ArtNr, uint16_t &ModuleAddress )
{
	ArtNr			 = g_uiArticleNumber;
	ModuleAddress	 = g_uiModuleAddress;

//	g_clDataPool.SetProgMode( true );

#ifdef DEBUGGING_PRINTOUT
	g_clDebugging.PrintLncvDiscoverStart( false, ArtNr, ModuleAddress  );
#endif

	return( LNCV_LACK_OK );
}


//**********************************************************************
//
int8_t notifyLNCVprogrammingStart( uint16_t &ArtNr, uint16_t &ModuleAddress )
{
	int8_t retval = -1;		//	default: ignore request
	
	if( g_uiArticleNumber == ArtNr )
	{
		if( 0xFFFF == ModuleAddress )
		{
			//-----------------------------------------------------
			//	valid article number, but broadcast address,
			//	so only give back Module Address
			//
//			g_clDataPool.SetProgMode( true );

			ModuleAddress	= g_uiModuleAddress;
			retval			= LNCV_LACK_OK;
		}
		else if( g_uiModuleAddress == ModuleAddress )
		{
			//-----------------------------------------------------
			//	valid article number and valid module address,
			//	so switch to programming mode
			//
			g_clDataPool.SetProgMode( true );

			retval	= LNCV_LACK_OK;
		}
	}

#ifdef DEBUGGING_PRINTOUT
	g_clDebugging.PrintLncvDiscoverStart( true, ArtNr, ModuleAddress  );
#endif

	return( retval );
}


//**********************************************************************
//
void notifyLNCVprogrammingStop( uint16_t ArtNr, uint16_t ModuleAddress )
{
#ifdef DEBUGGING_PRINTOUT
	g_clDebugging.PrintLncvStop();
#endif

	if( g_clDataPool.IsProgMode() )
	{
		if( 	(g_uiArticleNumber == ArtNr)
			&&	(g_uiModuleAddress == ModuleAddress) )
		{
			//------------------------------------------------------
			//	valid article number and valid module address,
			//	so switch off programming mode
			//
			g_clDataPool.SetProgMode( false );
		}
	}
}


//**********************************************************************
//
int8_t notifyLNCVread( uint16_t ArtNr, uint16_t Address, uint16_t &Value )
{
	int8_t retval = -1;		//	default: ignore request

	if( g_clDataPool.IsProgMode() && (g_uiArticleNumber == ArtNr) )
	{
		if( g_clLncvStorage.IsValidLNCVAddress( Address ) )
		{
			Value	= g_clLncvStorage.ReadLNCV( Address );
			retval	= LNCV_LACK_OK;
		}
		else
		{
			retval = LNCV_LACK_ERROR_UNSUPPORTED;
		}
	}

#ifdef DEBUGGING_PRINTOUT
	g_clDebugging.PrintLncvReadWrite( true, Address, Value );
#endif

	return( retval );
}


//**********************************************************************
//	notifyLNCVwrite
//----------------------------------------------------------------------
//	write the 'Value' into EEPROM, but only if the 'Address' is
//	NOT the article number address and NOT the version address
//
int8_t notifyLNCVwrite( uint16_t ArtNr, uint16_t Address, uint16_t Value )
{
	int8_t retval = -1;		//	default: ignore request

	if( g_clDataPool.IsProgMode() && (g_uiArticleNumber == ArtNr) )
	{
		if( g_clLncvStorage.IsValidLNCVAddress( Address ) )
		{
			if(		(LNCV_ADR_VERSION_NUMBER != Address)
				&&	(LNCV_ADR_ARTIKEL_NUMMER != Address) )
			{
				g_clLncvStorage.WriteLNCV( Address, Value );

				if( LNCV_ADR_MODULE_ADDRESS == Address )
				{
					g_uiModuleAddress = Value;
				}
			}

			retval = LNCV_LACK_OK;
		}
		else
		{
			retval = LNCV_LACK_ERROR_UNSUPPORTED;
		}
	}

#ifdef DEBUGGING_PRINTOUT
	g_clDebugging.PrintLncvReadWrite( false, Address, Value );
#endif

	return( retval );
}
