nh-finescale/ln2block/src/Loconet2Block/anfangsfeld.cpp

//##########################################################################
//#
//#		AnfangsfeldClass
//#
//#	This class contains the state machine for 'Anfangsfeld'
//#
//#-------------------------------------------------------------------------
//#
//#	File version:	11		from: 23.10.2025
//#
//#	Bug Fix:
//#		-	change control of LEDs from pin number to mask
//#
//#-------------------------------------------------------------------------
//#
//#	File version:	10		from: 02.08.2025
//#
//#	Implementation:
//#		-	add two LNCV addresses to differentiate between the sounds
//#			for Erlaubniswechsel, Vor- and Rueckblock
//#			change in function
//#				CheckState()
//#
//#-------------------------------------------------------------------------
//#
//#	File version:	9		from: 08.07.2025
//#
//#	Bug Fix:
//#		-	improvement of key box handling
//#			switch off of key permission whenever no "Ausfahrt" possible
//#			instead of only when "KEY_BOX_DIRECT" is configured
//#			change in function
//#				CheckState()
//#
//#-------------------------------------------------------------------------
//#
//#	File version:	8		from: 21.08.2024
//#
//#	Implementation:
//#		-	improvement of button handling
//#			reset of button states moved to 'Loconet2Block.ino'
//#			change in function
//#				CheckState()
//#
//#-------------------------------------------------------------------------
//#
//#	File version:	7		from: 16.01.2022
//#
//#	Bug Fix:
//#		-	Das 'Merken' von Tasten-Nachrichten führte immer wieder zu
//#			Problemen, wie z.B.: 'automatisches' Auslösen eines State-
//#			Wechsels. Dieses Problem ist nun behoben.
//#
//#-------------------------------------------------------------------------
//#
//#	File version:	6		from: 05.01.2022
//#
//#	Bug Fix:
//#		-	Die Ansteuerung des Anrückmelders war nicht in Ordnung.
//#			Sie funktioniert jetzt wie gewünscht.
//#
//#-------------------------------------------------------------------------
//#
//#	File version:	5		from: 29.12.2021
//#
//#	Implementation:
//#		-	Die Grüne LED zeigt nun den Zustand "Block belegt" an.
//#
//#-------------------------------------------------------------------------
//#
//#	File version:	4		from: 01.12.2021
//#
//#	Bug Fix:
//#		-	Im Zustand "ANFANGSFELD_STATE_FLUEGEL_KUPPLUNG" wird nun für
//#			den Felderblock die Auswertung der Nachrichten richtig
//#			verarbeitet.
//#
//#-------------------------------------------------------------------------
//#
//#	File version:	3		from: 15.11.2021
//#
//#	Implementation:
//#		-	Im Zustand "ANFANGSFELD_STATE_FLUEGEL_KUPPLUNG" wird nun,
//#			wenn das Konfig-Bit "FELDERBLOCK" gesetzt ist, kein
//#			automatischer Vorblock mehr gesendet.
//#			Stattdessen wird darauf gewartet, dass der Gleiskontakt wieder
//#			frei ist und dann "Hilfsvorblock" empfangen wurde.
//#
//#-------------------------------------------------------------------------
//#
//#	File version:	2		from: 13.10.2021
//#
//#	Bug Fix:
//#		-	Im Zustand "ANFANGSFELD_STATE_FAHRT" war die Abfrage für
//#			Einfahrkontakt oder Ausfahrkontakt fehlerhaft.
//#			Dies ist nun korrigiert.
//#
//#-------------------------------------------------------------------------
//#
//#	File version:	1		from: 14.09.2021
//#
//#	Implementation:
//#		-	first working version
//#
//##########################################################################


//==========================================================================
//
//		I N C L U D E S
//
//==========================================================================

#include "compile_options.h"

#include <Arduino.h>

#ifdef DEBUGGING_PRINTOUT
#include "debugging.h"
#endif

#include "anfangsfeld.h"
#include "data_pool.h"
#include "block_msg.h"
#include "io_control.h"


//==========================================================================
//
//		D E F I N I T I O N S
//
//==========================================================================


//==========================================================================
//
//		G L O B A L   V A R I A B L E S
//
//==========================================================================

AnfangsfeldClass	g_clAnfangsfeld		= AnfangsfeldClass();


//==========================================================================
//
//		C L A S S   F U N C T I O N S
//
//==========================================================================


///////////////////////////////////////////////////////////////////////
//	CLASS: AnfangsfeldClass
//

//*****************************************************************
//	Constructor
//-----------------------------------------------------------------
//	set the internal variables to their initial value
//	the initial state is 'ANFANGSFELD_STATE_FREI'.
//
//	IMPORTANT
//	'm_eOldState' must differ from 'm_eState' to perform
//	all actions for the initial state
//
AnfangsfeldClass::AnfangsfeldClass()
{
	m_eState				= ANFANGSFELD_STATE_FREI;
	m_eOldState				= ANFANGSFELD_STATE_FAHRT;
	m_ulAnfangsfeldMillis	= 0;
}

//*****************************************************************
//	CheckStates
//-----------------------------------------------------------------
//	This function is the heart of the state machine.
//	The data from the data pool and the current state are used
//	to check whether a state change should take place.
//-----------------------------------------------------------------
//	Principle of the state machine:
//	-	when entering a state (m_eOldState != m_eState)
//		actions are executed that are to be executed,
//		regardless of the previous state
//	-	in the state data from the data pool is checked
//		to find out whether a state change should take place.
//	-	if a state change should take place execute all actions
//		that are specific for this state change only.
//-----------------------------------------------------------------
//	RETURN-Wert
//		The actual or new state will be returned
//
anfangsfeld_state_t AnfangsfeldClass::CheckState( void )
{
	switch( m_eState )
	{
		//---------------------------------------------------------
		case ANFANGSFELD_STATE_FREI:
			if( m_eOldState != m_eState )
			{
				g_clDataPool.SetOutState(	OUT_MASK_FAHRT_MOEGLICH
										|	OUT_MASK_NICHT_ZWANGSHALT
										|	OUT_MASK_SCHLUESSELENTNAHME_MOEGLICH );
				g_clDataPool.ClearOutState(	OUT_MASK_AUSFAHRSPERRMELDER_TF71
										|	OUT_MASK_BLOCKMELDER_TF71
										|	OUT_MASK_VORBLOCKMELDER_RELAISBLOCK );

				g_clControl.LedOff( LED_GREEN );

#if PLATINE_VERSION > 3
				if( g_clLncvStorage.IsConfigSetAll( KEY_INTERFACE | KEY_BOX_DIRECT ) )
				{
					g_clControl.KeyRelaisOn();
					g_clControl.KeyLedOn();
				}
#endif

				m_eOldState = m_eState;

#ifdef DEBUGGING_PRINTOUT
				g_clDebugging.PrintAnfangsfeldState( ANFANGSFELD_STATE_FREI );
#endif
			}
			else if( g_clDataPool.IsOneInStateSet( IN_MASK_AUSFAHR_SIGNAL ) )
			{
				m_eState = ANFANGSFELD_STATE_FAHRT_PRE;
			}
			else if(	g_clDataPool.DarfHilfsvorblockSetzen()
					&&	g_clDataPool.IsOneInStateSet( IN_MASK_BEDIENUNG_HILFSVORBLOCK ) )
			{
				m_eState = ANFANGSFELD_STATE_BELEGT;
			}
			break;
			
		//---------------------------------------------------------
		case ANFANGSFELD_STATE_BELEGT:
			if( m_eOldState != m_eState )
			{
				g_clDataPool.SetSendBlockMessage( 1 << DP_BLOCK_MESSAGE_VORBLOCK );

				g_clDataPool.ClearOutState(	OUT_MASK_FAHRT_MOEGLICH
										|	OUT_MASK_NICHT_ZWANGSHALT
										|	OUT_MASK_SCHLUESSELENTNAHME_MOEGLICH
										|	OUT_MASK_WIEDERHOLSPERRMELDER_RELAISBLOCK );
				g_clDataPool.SetOutState(	OUT_MASK_BLOCKMELDER_TF71
										|	OUT_MASK_VORBLOCKMELDER_RELAISBLOCK );

				g_clControl.LedOn( LED_GREEN );

				if( g_clLncvStorage.IsConfigSet( KEY_INTERFACE ) )
				{
					g_clControl.KeyRelaisOff();
					g_clControl.KeyLedOff();
				}
				
				m_eOldState = m_eState;

#ifdef DEBUGGING_PRINTOUT
				g_clDebugging.PrintAnfangsfeldState( ANFANGSFELD_STATE_BELEGT );
#endif
			}
			else if( g_clDataPool.IsBlockMessageEmpfangen( 1 << DP_BLOCK_MESSAGE_RUECKBLOCK ) )
			{
				g_clDataPool.StartMelder( OUT_IDX_HUPE_RUECKBLOCK );

				m_eState = ANFANGSFELD_STATE_FREI;
			}
			break;
			
		//---------------------------------------------------------
		case ANFANGSFELD_STATE_FAHRT_PRE:
			if( m_eOldState != m_eState )
			{
				m_ulAnfangsfeldMillis	= millis() + cg_ulInterval_500_ms;	//	Timer starten
				m_eOldState				= m_eState;

				g_clDataPool.SetOutState(	OUT_MASK_AUSFAHRSPERRMELDER_TF71
										|	OUT_MASK_WIEDERHOLSPERRMELDER_RELAISBLOCK );
				g_clDataPool.ClearOutState(	OUT_MASK_SCHLUESSELENTNAHME_MOEGLICH );

				if( g_clLncvStorage.IsConfigSet( KEY_INTERFACE ) )
				{
					g_clControl.KeyRelaisOff();
					g_clControl.KeyLedOff();
				}

#ifdef DEBUGGING_PRINTOUT
				g_clDebugging.PrintAnfangsfeldState( ANFANGSFELD_STATE_FAHRT_PRE );
#endif
			}
			else if( millis() > m_ulAnfangsfeldMillis )
			{
				m_ulAnfangsfeldMillis = 0;

				g_clDataPool.ClearOutState( OUT_MASK_FAHRT_MOEGLICH );

				m_eState = ANFANGSFELD_STATE_FAHRT;
			}
			break;
			
		//---------------------------------------------------------
		case ANFANGSFELD_STATE_FAHRT:
			if( m_eOldState != m_eState )
			{
				m_eOldState = m_eState;

#ifdef DEBUGGING_PRINTOUT
				g_clDebugging.PrintAnfangsfeldState( ANFANGSFELD_STATE_FAHRT );
#endif
			}
			else if( g_clDataPool.IsOneInStateSet( IN_MASK_EINFAHR_SIGNAL ) )
			{
				m_eState = ANFANGSFELD_STATE_EINFAHR_SIGNAL;
			}
			else if( g_clDataPool.IsOneInStateSet(	IN_MASK_EINFAHR_KONTAKT
												|	IN_MASK_AUSFAHR_KONTAKT ) )
			{
				m_eState = ANFANGSFELD_STATE_FLUEGEL_KUPPLUNG;
			}
			else if( 	!g_clDataPool.IsOneInStateSet( IN_MASK_AUSFAHR_SIGNAL )
					&&	 g_clDataPool.IsOneInStateSet( IN_MASK_BEDIENUNG_HILFSVORBLOCK ) )
			{
				m_eState = ANFANGSFELD_STATE_BELEGT;
			}
			break;

		//---------------------------------------------------------
		case ANFANGSFELD_STATE_EINFAHR_SIGNAL:
			if( m_eOldState != m_eState )
			{
				m_eOldState = m_eState;

#ifdef DEBUGGING_PRINTOUT
				g_clDebugging.PrintAnfangsfeldState( ANFANGSFELD_STATE_EINFAHR_SIGNAL );
#endif
			}
			else if( !g_clDataPool.IsOneInStateSet( IN_MASK_EINFAHR_SIGNAL ) )
			{
				m_eState = ANFANGSFELD_STATE_FAHRT;
			}
			break;
			
		//---------------------------------------------------------
		case ANFANGSFELD_STATE_FLUEGEL_KUPPLUNG:
			if( m_eOldState != m_eState )
			{
				g_clDataPool.ClearOutState( OUT_MASK_NICHT_ZWANGSHALT );

				m_eOldState = m_eState;

#ifdef DEBUGGING_PRINTOUT
				g_clDebugging.PrintAnfangsfeldState( ANFANGSFELD_STATE_FLUEGEL_KUPPLUNG );
#endif
			}
			else if( !g_clDataPool.IsOneInStateSet( IN_MASK_AUSFAHR_SIGNAL ) )
			{
				//-------------------------------------------------
				//	Signal is back in Hp0
				//	check if a state change is required
				//
				if( g_clDataPool.IsOneOutStateSet( OUT_MASK_UEBERTRAGUNGSSTOERUNG ) )
				{
					m_eState = ANFANGSFELD_STATE_AUTO_VORBLOCK_GESTOERT;
				}
				else if( g_clLncvStorage.IsConfigSet( FELDERBLOCK ) )
				{
					//---------------------------------------------
					//	Felderblock
					//	no automatic VORBLOCK message
					//	wait for Hilfsvorblock message
					//
					if( g_clDataPool.IsOneInStateSet( IN_MASK_BEDIENUNG_HILFSVORBLOCK ) )
					{
						m_eState = ANFANGSFELD_STATE_BELEGT;
					}
				}
				else
				{
					//---------------------------------------------
					//	normal Block
					//	send automatic VORBLOCK message
					//
					m_eState = ANFANGSFELD_STATE_BELEGT;
				}
			}
			//-----------------------------------------------------
			//	Signal still NOT in Hp0
			//	so if someone pressed 'Hilfsvorblock' at this time
			//	then delete the flag to prevent an automatic
			//	VORBLOCK message when signal goes to Hp0
			//
			else if( g_clDataPool.IsOneInStateSet( IN_MASK_BEDIENUNG_HILFSVORBLOCK ) )
			{
				g_clDataPool.ClearInState( IN_MASK_BEDIENUNG_HILFSVORBLOCK );
			}
			break;
			
		//---------------------------------------------------------
		case ANFANGSFELD_STATE_AUTO_VORBLOCK_GESTOERT:
			if( m_eOldState != m_eState )
			{
				m_eOldState = m_eState;

#ifdef DEBUGGING_PRINTOUT
				g_clDebugging.PrintAnfangsfeldState( ANFANGSFELD_STATE_AUTO_VORBLOCK_GESTOERT );
#endif
			}
			else if( !g_clDataPool.IsOneOutStateSet( OUT_MASK_UEBERTRAGUNGSSTOERUNG ) )
			{
				if( g_clDataPool.IsOneInStateSet( IN_MASK_BEDIENUNG_HILFSVORBLOCK ) )
				{
					m_eState = ANFANGSFELD_STATE_BELEGT;
				}
			}
			break;
	}

	return( m_eState );
}
