nh-finescale/ln2block/src/Loconet2Block/debugging.cpp

//##########################################################################
//#
//#		DebuggingClass
//#
//#	Diese Klasse liefert Textausgaben an verschiedene Ausgabegeräte,
//#	z.B.: Serielle Schnittstelle oder OLED Display.
//#
//#-------------------------------------------------------------------------
//#
//#		OLED Display
//#
//#	the display can be switched between the following layouts:
//#		-	with Loconet and block messages
//#			 S                   1 1 1 1 1 1 1
//#			Z  0 1 2 3 4 5 6 7 8 9 0 1 2 3 4 5
//#			0    L N 2 B L   V x . m m . f f
//#			1  x H H H H   x H H H H H H H H
//#			2  E r l b : <Erlaubnis State>
//#			3  A f l d : <Anfangsfeld State>
//#			4  E f l d : <Endfeld State>
//#			5  S : 0 x 2 C     R : 0 x 9 0
//#			6  <Loconet messages>
//#			7  <Loconet message parameters>
//#
//#		-	with train numbers
//#			 S                   1 1 1 1 1 1 1
//#			Z  0 1 2 3 4 5 6 7 8 9 0 1 2 3 4 5
//#			0    L N 2 B L   V x . m m . f f
//#			1  x H H H H   x H H H H H H H H
//#			2  E r l b : <Erlaubnis State>
//#			3  A f l d : <Anfangsfeld State>
//#			4  E f l d : <Endfeld State>
//#			5  T r c k :   L   <ZN track>
//#			6  O f f r :   B   <ZN offer>
//#			7  A n n u :   L   <ZN annunciator>
//#
//#-------------------------------------------------------------------------
//#
//#	File version:	21		from: 28.04.2024
//#
//#	Bug Fix:
//#		-	parameters in function 'memcpy()' were swaped.
//#			change in function
//#				PrintTrainNumber()
//#
//#-------------------------------------------------------------------------
//#
//#	File version:	20		from: 12.11.2023
//#
//#	Implementation:
//#		-	switch to new OLED library => SimpleOled V1.2.1
//#			change in function
//#				Init()
//#
//#-------------------------------------------------------------------------
//#
//#	File version:	19		from: 10.08.2023
//#
//#	Implementation:
//#		-	add a check if a display is connected and if not don't send
//#			anything to the display
//#			new variable
//#				m_bDisplayPresent
//#			change in all functions
//#
//#-------------------------------------------------------------------------
//#
//#	File version:	18		from: 20.06.2023
//#
//#	Implementation:
//#		-	add functionality for the old style station interface
//#			new function
//#				PrintStationInterface()
//#
//#-------------------------------------------------------------------------
//#
//#	File version:	17		from: 16.05.2023
//#
//#	Implementation:
//#		-	new definition for function PrintTrainNumber()
//#				ZN_ALL	=>	clear all ZN fields
//#			changes in functions
//#				PrintTrainNumber()
//#
//#-------------------------------------------------------------------------
//#
//#	File version:	16		from: 06.03.2023
//#
//#	Bug Fix:
//#		-	wrong variable name when using the U8x8 library
//#			change in function
//#				PrintBlockOff()
//#		-	error when printing ZN numbers
//#			change in function
//#				PrintInfoLine()
//#				UpdateTrainNumber()
//#
//#-------------------------------------------------------------------------
//#
//#	File version:	15		from: 04.01.2023
//#
//#	Implementation:
//#		-	new order of display lines
//#		-	bitfield always visible
//#
//#-------------------------------------------------------------------------
//#
//#	File version:	14		from: 04.01.2023
//#
//#	Implementation:
//#		-	new Block Off printout
//#			new variable
//#				m_bBlockOn
//#
//#-------------------------------------------------------------------------
//#
//#	File version:	13		from: 15.12.2022
//#
//#	Bug Fix:
//#		-	train numbers were not shown on the display
//#			forget to check the flag m_bShowTrainNumbers in
//#			a lot of functions
//#
//#-------------------------------------------------------------------------
//#
//#	File version:	12		from: 09.12.2022
//#
//#	Implementation:
//#		-	streamlining debugging class
//#			remove function
//#				PrintText()
//#				PrintCounter()
//#				PrintMsgCount()
//#				PrintNotifySensorMsg()
//#
//#-------------------------------------------------------------------------
//#
//#	File version:	11		from: 24.11.2022
//#
//#	Implementation:
//#		-	only print information when data has changed
//#			changed function PrintDataPoolStatus()
//#		-	adjust all print texts to the same length
//#
//#-------------------------------------------------------------------------
//#
//#	File version:	10		from: 09.11.2022
//#
//#	Implementation:
//#		-	add usage of multiple devices with the same address
//#			changes in functions
//#				PrintNotifyType()
//#				PrintNotifyMsg()
//#
//#-------------------------------------------------------------------------
//#
//#	File version:	9		from: 02.10.2022
//#
//#	Implementation:
//#		-	change function 'PrintStorageCheck()' to print
//#				LNCV #0		module address
//#				LNCV #1		article number
//#
//#-------------------------------------------------------------------------
//#
//#	File version:	8		from: 26.08.2022
//#
//#	Implementation:
//#		-	support for U8x8lib added.
//#			new compiler switch 'USE_SIMPLE_LIB' in file compile_options.h
//#			if switch is set then the simple display library is used
//#			otherwise the U8x8lib is used.
//#
//#-------------------------------------------------------------------------
//#
//#	File version:	7		from: 05.03.2022
//#
//#	Implementation:
//#		-	change block message line to show the last send command
//#			and the last received command
//#		-	change function 'PrintSendBlockMsg()' to just have the
//#			command byte as parameter
//#
//#-------------------------------------------------------------------------
//#
//#	File version:	6		from: 26.02.2022
//#
//#	Implementation:
//#		-	change display library to simple_oled_sh1106 lib
//#
//#-------------------------------------------------------------------------
//#
//#	File version:	5		from: 26.02.2022
//#
//#	Implementation:
//#		-	Change version numbering
//#			the main version is now defined by the board version
//#			minor version is for new features
//#			bugfix is for changes in a feature
//#
//#-------------------------------------------------------------------------
//#
//#	File version:	4		from: 15.01.2022
//#
//#	Implementation:
//#		-	Es ist nun möglich, die Loconat-Nachrichten zu zählen und
//#			im Display anzeigen zu lassen.
//#			Gesteuert wird das ganz mit Hilfe von zwei Definitionen:
//#			-	#define COUNT_ALL_MESSAGES
//#			-	#define COUNT_MY_MESSAGES
//#			Wenn die Definition COUNT_ALL_MESSAGES aktiv ist, werden alle
//#			Nachrichten, die die Box erkennt gezählt und angezeigt.
//#			Wenn die Definition COUNT_MY_MESSAGES aktiv ist, werden nur
//#			die Nachrichten gezählt, die für die Box selber sind.
//#
//#-------------------------------------------------------------------------
//#
//#	File version:	3		from: 29.12.2021
//#
//#	Implementation:
//#		-	Eine neue Funktion hinzugefügt, die den "Block OFF" Zustand
//#			im Display anzeigt.
//#
//#-------------------------------------------------------------------------
//#
//#	File version:	2		from: 12.11.2021
//#
//#	Implementation:
//#		-	Das Display kann nun um 180 Grad gedreht werden.
//#			Dazu hat die Funktion "PrintTitle()" einen weitere Parameter
//#			'flipDisplay' bekommen, der die Drehung steuert.
//#			'0' =>	Display normal
//#			'1'	=>	Display gedreht
//#
//#-------------------------------------------------------------------------
//#
//#	File version:	1		from: 14.09.2021
//#
//#	Implementation:
//#		-	OLED Display
//#			The display has the following setup:
//#			 S                   1 1 1 1 1 1 1
//#			Z  0 1 2 3 4 5 6 7 8 9 0 1 2 3 4 5
//#			0    L N 2 B L   V x . m m . f f
//#			1  x H H H H   x H H H H H H H H
//#			2  E r l b : <Erlaubnis State>
//#			3  A f l d : <Anfangsfeld State>
//#			4  E f l d : <Endfeld State>
//#			5  S : 0 x 2 C     R : 0 x 9 0
//#			6  <Loconet messages>
//#			7  <Loconet message parameters>
//#
//##########################################################################


//==========================================================================
//
//		I N C L U D E S
//
//==========================================================================

#include "compile_options.h"


#ifdef DEBUGGING_PRINTOUT
//**************************************************************************
//**************************************************************************

#include <Arduino.h>
#include <avr/pgmspace.h>
#include <Wire.h>

#ifdef USE_SIMPLE_DISPLAY_LIB
	#include <SimpleOled.h>
#else
	#include <U8x8lib.h>
#endif

#include "debugging.h"
#include "block_msg.h"


//==========================================================================
//
//		D E F I N I T I O N S
//
//==========================================================================

#define BLINK_TIME					500


#define	DISPLAY_ADDRESS				60
#define SECOND_DISPLAY_ADDRESS		61

//----------------------------------------------------------------------
//	definition of display positions
//
#define BITFIELD_LINE				1
#define	BITFIELD_COLUMN				0
#define ERLAUBNIS_LINE				2
#define	ERLAUBNIS_COLUMN			5
#define	ANFANGSFELD_LINE			ERLAUBNIS_LINE + 1
#define	ANFANGSFELD_COLUMN			ERLAUBNIS_COLUMN
#define ENDFELD_LINE				ERLAUBNIS_LINE + 2
#define ENDFELD_COLUMN				ERLAUBNIS_COLUMN
#define BLOCK_MSG_LINE				5
#define BLOCK_MSG_SEND_COLUMN		0
#define BLOCK_MSG_RECEIVE_COLUMN	8
#define	LOCONET_MSG_LINE			6
#define LOCONET_MSG_COLUMN			0
#define INFO_LINE					7
#define INFO_COLUMN					0

#define ZN_TRACK_LINE				5
#define ZN_OFFER_LINE				6
#define ZN_ANNUNCIATOR_LINE			7
#define ZN_COLUMN					6

#define ZN_TEXT_LENGTH				8


//==========================================================================
//
//		G L O B A L   V A R I A B L E S
//
//==========================================================================

DebuggingClass	g_clDebugging	= DebuggingClass();

//----------------------------------------------------------------------
//	Variable für das OLED Display
//

#ifndef USE_SIMPLE_DISPLAY_LIB
U8X8_SH1106_128X64_NONAME_HW_I2C	u8x8( U8X8_PIN_NONE );
#endif

uint32_t	g_ulOldOutStatus	= 0x10000000L;
uint16_t	g_uiOldInStatus	= 0x1000;

char		g_chDebugString[ 18 ];
const char *g_chSwitch[] =
{
	"E_Sig     : ",
	"A_Sig     : ",
	"E_Kontakt : ",
	"A_Kontakt : ",
	"T_Rückblk : ",
	"T_H_Vorblk: ",
	"T_Erlbns  : ",
	"T_Ans_ON  : ",
	"T_Ans_OFF : ",
	"Key Free  : "
};

const char gc_strTrainNumberClear = { "        " };

uint8_t g_arTrainNumbers[ 3 ][ ZN_TEXT_LENGTH + 1 ] =
{
	"        ",
	"        ",
	"        "
};


//==========================================================================
//
//		C L A S S   F U N C T I O N S
//
//==========================================================================


////////////////////////////////////////////////////////////////////////
//	CLASS: DebuggingClass
//

//******************************************************************
//	Constructor
//
DebuggingClass::DebuggingClass()
{
	m_ulBlinkTime		= 0;
	m_bDisplayPresent	= false;
	m_bBlockOn			= true;
	m_bInvers			= true;
	m_bShowTrainNumbers	= false;
}


//******************************************************************
//	Init
//
void DebuggingClass::Init( void )
{
	uint8_t	usError;
	uint8_t	usAdr		= DISPLAY_ADDRESS;


	//------------------------------------------------------------------
	//	Check if Display can be connected under the given address
	//
	Wire.begin();
	Wire.beginTransmission( usAdr );
	usError = Wire.endTransmission();

	if( 0 == usError )
	{
		m_bDisplayPresent = true;
	}
	else
	{
		usAdr = SECOND_DISPLAY_ADDRESS;

		Wire.beginTransmission( usAdr );
		usError = Wire.endTransmission();

		if( 0 == usError )
		{
			m_bDisplayPresent = true;
		}
	}

	Wire.end();

	if( m_bDisplayPresent )
	{

#ifdef USE_SIMPLE_DISPLAY_LIB

		//g_clDisplay.Init( CHIP_TYPE_SSD1306, usAdr );
		g_clDisplay.Init( CHIP_TYPE_SH1106, usAdr );

#else

		u8x8.setI2CAddress( usAdr );
		u8x8.begin();
		u8x8.setFont( u8x8_font_chroma48medium8_r );

#endif

	}

	delay( 50 );
}


//******************************************************************
//	PrintTitle
//
void DebuggingClass::Loop( void )
{
	if( m_bDisplayPresent && m_bBlockOn && m_bShowTrainNumbers )
	{
		if( millis() > m_ulBlinkTime )
		{
			m_ulBlinkTime = millis() + BLINK_TIME;
			m_bInvers     = !m_bInvers;
			
			UpdateTrainNumber( ZN_TRACK );
			UpdateTrainNumber( ZN_OFFER );
			UpdateTrainNumber( ZN_ANNUNCIATOR );
		}
	}
}


//******************************************************************
//	PrintTitle
//
void DebuggingClass::PrintTitle(	uint8_t versionMain,
									uint8_t versionMinor,
									uint8_t versionBugFix,
									bool	flipDisplay		)
{
	if( m_bDisplayPresent )
	{

#ifdef USE_SIMPLE_DISPLAY_LIB

		g_clDisplay.Clear();
		g_clDisplay.Flip( flipDisplay );
		g_clDisplay.SetInverseFont( true );
		sprintf( g_chDebugString, " LN2BL V%d.%02d.%02d ",
				versionMain, versionMinor, versionBugFix );
		g_clDisplay.Print( g_chDebugString );
		g_clDisplay.SetInverseFont( false );

#else

		u8x8.clear();
		u8x8.setFlipMode( (flipDisplay ? 1 : 0) );
		u8x8.setInverseFont( 1 );
		sprintf( g_chDebugString, " LN2BL V%d.%02d.%02d ",
				versionMain, versionMinor, versionBugFix );
		u8x8.print( g_chDebugString );
		u8x8.setInverseFont( 0 );

#endif

	}
}


//******************************************************************
//	PrintInfoLine
//
void DebuggingClass::PrintStationInterface( bool bInterfaceConnected )
{
	if( m_bDisplayPresent )
	{

#ifdef USE_SIMPLE_DISPLAY_LIB

		g_clDisplay.Print( F( "  Intrfc: " ) );
		g_clDisplay.Print( (bInterfaceConnected ? "yes\n" : "no \n") );

#else

		u8x8.print( F( "  Intrfc: " ) );
		u8x8.print( (bInterfaceConnected ? "yes\n" : "no\n") );

#endif

	}
}


//******************************************************************
//	PrintInfoLine
//
void DebuggingClass::PrintInfoLine( info_lines_t number )
{
	if( m_bDisplayPresent )
	{

#ifdef USE_SIMPLE_DISPLAY_LIB

		switch( number )
		{
			case infoLineFields:
				g_clDisplay.SetCursor( ERLAUBNIS_LINE, 0 );
				g_clDisplay.Print( F( "Erlb:\nAfld:\nEfld:" ) );
				break;

			case infoLineInit:
				g_clDisplay.Print( F( "\n  Init:\n" ) );
				break;

			case infoLineLedTest:
				g_clDisplay.Print( F( "  LED Test\n" ) );
				break;

			case infoLineMessages:
				m_bShowTrainNumbers = false;

			case infoLineTrainNumbers:
				m_ulBlinkTime = 0L;
				g_clDisplay.ClearLine( ZN_TRACK_LINE );
				g_clDisplay.ClearLine( ZN_OFFER_LINE );
				g_clDisplay.ClearLine( ZN_ANNUNCIATOR_LINE );

				if( infoLineMessages == number )
				{
					break;
				}

				g_clDisplay.SetCursor( ZN_TRACK_LINE, 0 );
				g_clDisplay.Print( F( "Trck:\nOffr:\nAnnu:" ) );
				m_bShowTrainNumbers = true;
				m_bInvers			= true;
				break;

			default:
				break;
		}

#else

		switch( number )
		{
			case infoLineFields:
				u8x8.setCursor( 0, ERLAUBNIS_LINE );
				u8x8.print( F( "Erlb:\nAfld:\nEfld:" ) );
				break;

			case infoLineInit:
				u8x8.print( F( "\n  Init:\n" ) );
				break;

			case infoLineLedTest:
				u8x8.print( F( "  LED Test\n" ) );
				break;

			case infoLineMessages:
				m_bShowTrainNumbers = false;

			case infoLineTrainNumbers:
				m_ulBlinkTime = 0L;
				u8x8.clearLine( ZN_TRACK_LINE );
				u8x8.clearLine( ZN_OFFER_LINE );
				u8x8.clearLine( ZN_ANNUNCIATOR_LINE );

				if( infoLineMessages == number )
				{
					break;
				}

				u8x8.setCursor( 0, ZN_TRACK_LINE );
				u8x8.print( F( "Trck:\nOffr:\nAnnu:" ) );
				m_bShowTrainNumbers = true;
				m_bInvers			= true;
				break;

			default:
				break;
		}

#endif

	}
}


//******************************************************************
//	PrintBlockOff
//
void DebuggingClass::PrintBlockOff( void )
{
	m_bBlockOn = false;

	if( m_bDisplayPresent )
	{

#ifdef USE_SIMPLE_DISPLAY_LIB

		for( uint8_t idx = INFO_LINE ; ERLAUBNIS_LINE <= idx ; idx-- )
		{
			g_clDisplay.ClearLine( idx );
		}

		g_clDisplay.SetInverseFont( true );
		g_clDisplay.Print( F( "\n                \n  Block is OFF  \n                " ) );
		g_clDisplay.SetInverseFont( false );

#else

		for( uint8_t idx = INFO_LINE ; ERLAUBNIS_LINE <= idx ; idx-- )
		{
			u8x8.clearLine( idx );
		}

		u8x8.setCursor( INFO_COLUMN, ANFANGSFELD_LINE );
		u8x8.setInverseFont( 1 );
		u8x8.print( F( "                \n  Block is OFF  \n                " ) );
		u8x8.setInverseFont( 0 );

#endif

	}
}


//******************************************************************
//	PrintErlaubnisState
//
void DebuggingClass::PrintErlaubnisState( erlaubnis_state_t state )
{
	if( m_bDisplayPresent && m_bBlockOn )
	{

#ifdef USE_SIMPLE_DISPLAY_LIB

		g_clDisplay.SetCursor( ERLAUBNIS_LINE, ERLAUBNIS_COLUMN );

		switch( state )
		{
			case ERLAUBNIS_STATE_KEINER:
				g_clDisplay.Print( F( "keiner" ) );
				break;
				
			case ERLAUBNIS_STATE_ERHALTEN:
				g_clDisplay.Print( F( "erhalten " ) );
				break;
				
			case ERLAUBNIS_STATE_ABGEGEBEN_PRE:
				g_clDisplay.Print( F( "abgeg pre" ) );
				break;
				
			case ERLAUBNIS_STATE_ABGEGEBEN:
				g_clDisplay.Print( F( "abgegeben" ) );
				break;
		}

#else

		u8x8.setCursor( ERLAUBNIS_COLUMN, ERLAUBNIS_LINE );

		switch( state )
		{
			case ERLAUBNIS_STATE_KEINER:
				u8x8.print( F( "keiner" ) );
				break;
				
			case ERLAUBNIS_STATE_ERHALTEN:
				u8x8.print( F( "erhalten " ) );
				break;
				
			case ERLAUBNIS_STATE_ABGEGEBEN_PRE:
				u8x8.print( F( "abgeg pre" ) );
				break;
				
			case ERLAUBNIS_STATE_ABGEGEBEN:
				u8x8.print( F( "abgegeben" ) );
				break;
		}

#endif

	}
}


//******************************************************************
//	PrintAnfangsfeldState
//
void DebuggingClass::PrintAnfangsfeldState( anfangsfeld_state_t state )
{
	if( m_bDisplayPresent && m_bBlockOn )
	{

#ifdef USE_SIMPLE_DISPLAY_LIB

		g_clDisplay.SetCursor( ANFANGSFELD_LINE, ANFANGSFELD_COLUMN );

		switch( state )
		{
			case ANFANGSFELD_STATE_FREI:
				g_clDisplay.Print( F( "frei     " ) );
				break;

			case ANFANGSFELD_STATE_BELEGT:
				g_clDisplay.Print( F( "belegt   " ) );
				break;

			case ANFANGSFELD_STATE_FAHRT_PRE:
				g_clDisplay.Print( F( "fahrt pre" ) );
				break;

			case ANFANGSFELD_STATE_FAHRT:
				g_clDisplay.Print( F( "fahrt    " ) );
				break;

			case ANFANGSFELD_STATE_EINFAHR_SIGNAL:
				g_clDisplay.Print( F( "einfahrt " ) );
				break;

			case ANFANGSFELD_STATE_FLUEGEL_KUPPLUNG:
				g_clDisplay.Print( F( "fluegelkp" ) );
				break;

			case ANFANGSFELD_STATE_AUTO_VORBLOCK_GESTOERT:
				g_clDisplay.Print( F( "auto err " ) );
				break;
		}

#else

		u8x8.setCursor( ANFANGSFELD_COLUMN, ANFANGSFELD_LINE );

		switch( state )
		{
			case ANFANGSFELD_STATE_FREI:
				u8x8.print( F( "frei     " ) );
				break;

			case ANFANGSFELD_STATE_BELEGT:
				u8x8.print( F( "belegt   " ) );
				break;

			case ANFANGSFELD_STATE_FAHRT_PRE:
				u8x8.print( F( "fahrt pre" ) );
				break;

			case ANFANGSFELD_STATE_FAHRT:
				u8x8.print( F( "fahrt    " ) );
				break;

			case ANFANGSFELD_STATE_EINFAHR_SIGNAL:
				u8x8.print( F( "einfahrt " ) );
				break;

			case ANFANGSFELD_STATE_FLUEGEL_KUPPLUNG:
				u8x8.print( F( "fluegelkp" ) );
				break;

			case ANFANGSFELD_STATE_AUTO_VORBLOCK_GESTOERT:
				u8x8.print( F( "auto err " ) );
				break;
		}

#endif

	}
}


//******************************************************************
//	PrintEndfeldState
//
void DebuggingClass::PrintEndfeldState( endfeld_state_t state )
{
	if( m_bDisplayPresent && m_bBlockOn )
	{

#ifdef USE_SIMPLE_DISPLAY_LIB

		g_clDisplay.SetCursor( ENDFELD_LINE, ENDFELD_COLUMN );

		switch( state )
		{
			case ENDFELD_STATE_FREI_BOOT:
				g_clDisplay.Print( F( "frei boot" ) );
				break;

			case ENDFELD_STATE_FREI:
				g_clDisplay.Print( F( "frei     " ) );
				break;

			case ENDFELD_STATE_BELEGT:
				g_clDisplay.Print( F( "belegt   " ) );
				break;

			case ENDFELD_STATE_SIGNAL_GEZOGEN:
				g_clDisplay.Print( F( "signal   " ) );
				break;

			case ENDFELD_STATE_ANSCHALTER_AKTIV:
				g_clDisplay.Print( F( "anschalt " ) );
				break;

			case ENDFELD_STATE_ERSTE_ACHSE:
				g_clDisplay.Print( F( "1. achse " ) );
				break;

			case ENDFELD_STATE_GERAEUMT:
				g_clDisplay.Print( F( "geraeumt " ) );
				break;
		}

#else

		u8x8.setCursor( ENDFELD_COLUMN, ENDFELD_LINE );

		switch( state )
		{
			case ENDFELD_STATE_FREI_BOOT:
				u8x8.print( F( "frei boot" ) );
				break;

			case ENDFELD_STATE_FREI:
				u8x8.print( F( "frei     " ) );
				break;

			case ENDFELD_STATE_BELEGT:
				u8x8.print( F( "belegt   " ) );
				break;

			case ENDFELD_STATE_SIGNAL_GEZOGEN:
				u8x8.print( F( "signal   " ) );
				break;

			case ENDFELD_STATE_ANSCHALTER_AKTIV:
				u8x8.print( F( "anschalt " ) );
				break;

			case ENDFELD_STATE_ERSTE_ACHSE:
				u8x8.print( F( "1. achse " ) );
				break;

			case ENDFELD_STATE_GERAEUMT:
				u8x8.print( F( "geraeumt " ) );
				break;
		}

#endif

	}
}


//******************************************************************
//	PrintSendBlockMsg
//
void DebuggingClass::PrintSendBlockMsg( uint8_t msg )
{
	if( m_bDisplayPresent && m_bBlockOn && !m_bShowTrainNumbers )
	{

#ifdef USE_SIMPLE_DISPLAY_LIB

		g_clDisplay.SetCursor( BLOCK_MSG_LINE, BLOCK_MSG_SEND_COLUMN );
		sprintf( g_chDebugString, "S:0x%02X", msg );
		g_clDisplay.Print( g_chDebugString );

#else

		u8x8.setCursor( BLOCK_MSG_SEND_COLUMN, BLOCK_MSG_LINE );
		sprintf( g_chDebugString, "S:0x%02X", msg );
		u8x8.print( g_chDebugString );

#endif

	}
}


//******************************************************************
//	PrintReceiveBlockMsg
//
void DebuggingClass::PrintReceiveBlockMsg( uint8_t msg )
{
	if( m_bDisplayPresent && m_bBlockOn && !m_bShowTrainNumbers )
	{

#ifdef USE_SIMPLE_DISPLAY_LIB

		g_clDisplay.SetCursor( BLOCK_MSG_LINE, BLOCK_MSG_RECEIVE_COLUMN );
		sprintf( g_chDebugString, "R:0x%02X", msg );
		g_clDisplay.Print( g_chDebugString );

#else

		u8x8.setCursor( BLOCK_MSG_RECEIVE_COLUMN, BLOCK_MSG_LINE );
		sprintf( g_chDebugString, "R:0x%02X", msg );
		u8x8.print( g_chDebugString );

#endif

	}
}


//******************************************************************
//	PrintReportSensorMsg
//
void DebuggingClass::PrintReportSensorMsg( uint16_t address, uint8_t state )
{
	if( m_bDisplayPresent && m_bBlockOn && !m_bShowTrainNumbers )
	{

#ifdef USE_SIMPLE_DISPLAY_LIB

		SetLncvMsgPos();
		g_clDisplay.Print( F( "S:Report Sensor\n" ) );
		sprintf( g_chDebugString, "Adr:%5d Dir:%d", address, state );
		g_clDisplay.Print( g_chDebugString );

#else

		SetLncvMsgPos();
		u8x8.print( F( "S:Report Sensor\n" ) );
		sprintf( g_chDebugString, "Adr:%5d Dir:%d", address, state );
		u8x8.print( g_chDebugString );

#endif

	}
}


//******************************************************************
//	PrintReportSwitchMsg
//
void DebuggingClass::PrintReportSwitchMsg( uint16_t address, uint8_t switchDir )
{
	if( m_bDisplayPresent && m_bBlockOn && !m_bShowTrainNumbers )
	{

#ifdef USE_SIMPLE_DISPLAY_LIB

		SetLncvMsgPos();
		g_clDisplay.Print( F( "Request Switch\n" ) );
		sprintf( g_chDebugString, "Adr:%5d Dir:%d", address, switchDir );
		g_clDisplay.Print( g_chDebugString );

#else

		SetLncvMsgPos();
		u8x8.print( F( "Request Switch\n" ) );
		sprintf( g_chDebugString, "Adr:%5d Dir:%d", address, switchDir );
		u8x8.print( g_chDebugString );

#endif

	}
}


//******************************************************************
//	PrintReportSwitch
//
void DebuggingClass::PrintNotifyType( notify_type_t type )
{
	if( m_bDisplayPresent && m_bBlockOn && !m_bShowTrainNumbers )
	{

#ifdef USE_SIMPLE_DISPLAY_LIB

		g_clDisplay.SetCursor( LOCONET_MSG_LINE, LOCONET_MSG_COLUMN );

		switch( type )
		{
			case NT_Sensor:
				g_clDisplay.Print( F( "R:Sensor       " ) );
				break;

			case NT_Request:
				g_clDisplay.Print( F( "R:Switch Reqst " ) );
				break;

			case NT_Report:
				g_clDisplay.Print( F( "R:Switch Report" ) );
				break;

			case NT_State:
				g_clDisplay.Print( F( "R:Switch State " ) );
				break;
		}

#else

		u8x8.setCursor( LOCONET_MSG_COLUMN, LOCONET_MSG_LINE );

		switch( type )
		{
			case NT_Sensor:
				u8x8.print( F( "R:Sensor       " ) );
				break;

			case NT_Request:
				u8x8.print( F( "R:Switch Reqst " ) );
				break;

			case NT_Report:
				u8x8.print( F( "R:Switch Report" ) );
				break;

			case NT_State:
				u8x8.print( F( "R:Switch State " ) );
				break;
		}

#endif

	}
}


//******************************************************************
//	PrintNotifySwitchMsg
//
void DebuggingClass::PrintNotifyMsg( uint8_t idx, uint16_t address, uint8_t dir, uint8_t output  )
{
	if( m_bDisplayPresent && m_bBlockOn && !m_bShowTrainNumbers )
	{

#ifdef USE_SIMPLE_DISPLAY_LIB

		g_clDisplay.SetCursor( INFO_LINE, INFO_COLUMN );
		g_clDisplay.Print( g_chSwitch[ idx ] );
		g_clDisplay.Print( (dir ? "1  " : "0  ") );

#else

		u8x8.setCursor( INFO_COLUMN, INFO_LINE );
		u8x8.print( g_chSwitch[ idx ] );
		u8x8.print( (dir ? "1  " : "0  ") );

#endif

	}
}


//******************************************************************
//	PrintLncvDiscoverStart
//
void DebuggingClass::PrintLncvDiscoverStart( bool start, uint16_t artikel, uint16_t address )
{
	if( m_bDisplayPresent )
	{
		SetLncvMsgPos();

#ifdef USE_SIMPLE_DISPLAY_LIB

		if( start )
		{
			g_clDisplay.Print( F( "LNCV Prog Start\n" ) );
		}
		else
		{
			g_clDisplay.Print( F( "LNCV Discover\n" ) );
		}

		sprintf( g_chDebugString, "AR%5d AD%5d", artikel, address );
		g_clDisplay.Print( g_chDebugString );

#else

		if( start )
		{
			u8x8.print( F( "LNCV Prog Start\n" ) );
		}
		else
		{
			u8x8.print( F( "LNCV Discover\n" ) );
		}

		sprintf( g_chDebugString, "AR%5d AD%5d", artikel, address );
		u8x8.print( g_chDebugString );

#endif

	}
}


//******************************************************************
//	PrintLncvStop
//
void DebuggingClass::PrintLncvStop()
{
	if( m_bDisplayPresent )
	{

#ifdef USE_SIMPLE_DISPLAY_LIB

		SetLncvMsgPos();
		g_clDisplay.Print( F( "LNCV Prog Stop" ) );

#else

		SetLncvMsgPos();
		u8x8.print( F( "LNCV Prog Stop" ) );

#endif

	}
}


//******************************************************************
//	PrintLncvReadWrite
//
void DebuggingClass::PrintLncvReadWrite( bool doRead, uint16_t address, uint16_t value )
{
	if( m_bDisplayPresent )
	{
		SetLncvMsgPos();

#ifdef USE_SIMPLE_DISPLAY_LIB

		if( doRead )
		{
			g_clDisplay.Print( F( "LNCV Read\n" ) );
		}
		else
		{
			g_clDisplay.Print( F( "LNCV Write\n" ) );
		}

		sprintf( g_chDebugString, "AD%5d VA%5d", address, value );
		g_clDisplay.Print( g_chDebugString );

#else

		if( doRead )
		{
			u8x8.print( F( "LNCV Read\n" ) );
		}
		else
		{
			u8x8.print( F( "LNCV Write\n" ) );
		}

		sprintf( g_chDebugString, "AD%5d VA%5d", address, value );
		u8x8.print( g_chDebugString );

#endif

	}
}


//******************************************************************
//	SetLncvMsgPos
//
void DebuggingClass::SetLncvMsgPos( void )
{
	if( m_bDisplayPresent )
	{

#ifdef USE_SIMPLE_DISPLAY_LIB

		g_clDisplay.ClearLine( LOCONET_MSG_LINE + 1 );
		g_clDisplay.ClearLine( LOCONET_MSG_LINE );

#else

		u8x8.clearLine( LOCONET_MSG_LINE );
		u8x8.clearLine( LOCONET_MSG_LINE + 1 );
		u8x8.setCursor( LOCONET_MSG_COLUMN, LOCONET_MSG_LINE );

#endif

	}
}


//******************************************************************
//	PrintStorageCheck
//
void DebuggingClass::PrintStorageCheck( uint16_t uiAddress, uint16_t uiArticle )
{
	if( m_bDisplayPresent )
	{

#ifdef USE_SIMPLE_DISPLAY_LIB

		g_clDisplay.Print( F( "Check EEPROM:\n" ) );
		sprintf( g_chDebugString, " 0:%05d 1:%05d", uiAddress, uiArticle );
		g_clDisplay.Print( g_chDebugString );

#else

		u8x8.print( F( "  Check EEPROM:\n" ) );
		sprintf( g_chDebugString, " 0:%05d 1:%05d", uiAddress, uiArticle );
		u8x8.print( g_chDebugString );

#endif

	}
}


//******************************************************************
//	PrintStorageDefault
//
void DebuggingClass::PrintStorageDefault( void )
{
	if( m_bDisplayPresent )
	{

#ifdef USE_SIMPLE_DISPLAY_LIB

		g_clDisplay.Print( F( "\nSet default Adr" ) );

#else

		u8x8.print( F( "\nSet default Adr" ) );

#endif

	}
}


//******************************************************************
//	PrintStorageRead
//
void DebuggingClass::PrintStorageRead( void )
{
	if( m_bDisplayPresent )
	{

#ifdef USE_SIMPLE_DISPLAY_LIB

		g_clDisplay.Print( F( "\n Lese LNCVs\n" ) );

#else

		u8x8.print( F( "\n Lese LNCVs\n" ) );

#endif

	}
}


//******************************************************************
//	PrintDataPoolStatus
//
void DebuggingClass::PrintDataPoolStatus( uint16_t loconetIn, uint32_t loconetOut )
{
	uint16_t	lowOut	= loconetOut;
	uint16_t	highOut	= (loconetOut >> 16);

	if( m_bDisplayPresent )
	{
		if(		(g_uiOldInStatus  != loconetIn)
			||	(g_ulOldOutStatus != loconetOut) )
		{
			g_uiOldInStatus  = loconetIn;
			g_ulOldOutStatus = loconetOut;

#ifdef USE_SIMPLE_DISPLAY_LIB

			g_clDisplay.SetCursor( BITFIELD_LINE, BITFIELD_COLUMN );
			sprintf( g_chDebugString, "x%04X x%04X%04X", loconetIn, highOut, lowOut );
			g_clDisplay.Print( g_chDebugString );
//			g_clDisplay.SetCursor( BITFIELD_LINE, BITFIELD_COLUMN + 1 );
//			sprintf( g_chDebugString, "0x%02X", m_uiBlockIn );
//			g_clDisplay.Print( g_chDebugString );

#else

			u8x8.setCursor( BITFIELD_COLUMN, BITFIELD_LINE );
			sprintf( g_chDebugString, "x%04X x%04X%04X", loconetIn, highOut, lowOut );
			u8x8.print( g_chDebugString );
//			u8x8.setCursor( BITFIELD_COLUMN, BITFIELD_LINE + 1 );
//			sprintf( g_chDebugString, "0x%02X", m_uiBlockIn );
//			u8x8.print( g_chDebugString );

#endif

		}
	}
}


//******************************************************************
//	PrintTrainNumber
//
void DebuggingClass::PrintTrainNumber( uint8_t usIdx, uint8_t *pText )
{
	if( m_bDisplayPresent )
	{
		if( ZN_ALL == usIdx )
		{
			memcpy( &g_arTrainNumbers[ ZN_TRACK       ][ 0 ], gc_strTrainNumberClear, ZN_TEXT_LENGTH );
			memcpy( &g_arTrainNumbers[ ZN_OFFER       ][ 0 ], gc_strTrainNumberClear, ZN_TEXT_LENGTH );
			memcpy( &g_arTrainNumbers[ ZN_ANNUNCIATOR ][ 0 ], gc_strTrainNumberClear, ZN_TEXT_LENGTH );
		}
		else
		{
			for( uint8_t idx = 0 ; ZN_TEXT_LENGTH > idx ; idx++ )
			{
				g_arTrainNumbers[ usIdx ][ idx ] = *pText;
				pText++;
			}
		}
	}
}


//******************************************************************
//	UpdateTrainNumber
//
void DebuggingClass::UpdateTrainNumber( uint8_t usIdx )
{
	uint8_t *	pHelper = &g_arTrainNumbers[ usIdx ][ 0 ];
	uint8_t		theChar;
	uint8_t		bInvert;

	if( m_bDisplayPresent )
	{

#ifdef USE_SIMPLE_DISPLAY_LIB

		g_clDisplay.SetCursor( ZN_TRACK_LINE + usIdx, ZN_COLUMN );
		g_clDisplay.PrintChar( *pHelper++ );
		g_clDisplay.PrintChar( *pHelper++ );

		for( uint8_t idx = 2 ; ZN_TEXT_LENGTH > idx ; idx++ )
		{
			bInvert = 0x80 & *pHelper;
			theChar = 0x7F & *pHelper;
			pHelper++;

			if( bInvert && m_bInvers )
			{
				g_clDisplay.SetInverseFont( true );
			}

			g_clDisplay.PrintChar( theChar );

			if( bInvert && m_bInvers )
			{
				g_clDisplay.SetInverseFont( false );
			}
		}

#else

		uint8_t	usLine		= ZN_TRACK_LINE + usIdx;
		uint8_t	usColumn	= ZN_COLUMN;

		u8x8.drawGlyph( usColumn++, usLine, *pHelper++ );
		u8x8.drawGlyph( usColumn++, usLine, *pHelper++ );

		for( uint8_t idx = 2 ; ZN_TEXT_LENGTH > idx ; idx++ )
		{
			bInvert = 0x80 & *pHelper;
			theChar = 0x7F & *pHelper;
			pHelper++;

			if( bInvert && m_bInvers )
			{
				u8x8.setInverseFont( 1 );
			}

			u8x8.drawGlyph( usColumn++, usLine, theChar );

			if( bInvert && m_bInvers )
			{
				u8x8.setInverseFont( 0 );
			}
		}

#endif

	}
}


//**************************************************************************
//**************************************************************************
#endif	//	DEBUGGING_PRINTOUT
