nh-finescale/ln2block/src/Loconet2Block/block_msg.h

#pragma once

//##########################################################################
//#
//#		block_msg
//#
//#	definitions for block messages and block message protocol
//#
//#-------------------------------------------------------------------------
//#
//#	File version:	4		from: 28.12.2025
//#
//#	Implementation:
//#		-	add message code for signal aspect (BLOCK_MSG_DISTANT_SIGNAL)
//#
//#-------------------------------------------------------------------------
//#
//#	File version:	3		from: 03.02.2023
//#
//#	Implementation:
//#		-	add new message code (BLOCK_MSG_TRAIN_NUMBER)
//#
//#-------------------------------------------------------------------------
//#
//#	File version:	2		from: 25.02.2022
//#
//#	Implementation:
//#		-	add new message code (BLOCK_MSG_BROADCAST)
//#
//#-------------------------------------------------------------------------
//#
//#	File version:	1		from: 31.01.2022
//#
//#	Implementation:
//#		-	first working version
//#
//##########################################################################


//==========================================================================
//
//		I N C L U D E S
//
//==========================================================================


//==========================================================================
//
//		D E F I N I T I O N S
//
//==========================================================================

#define SLIP_END						0xC0
#define SLIP_ESC						0xDB
#define SLIP_ESC_END					0xDC
#define SLIP_ESC_ESC					0xDD

#define BLOCK_MSG_VORBLOCK				0x2A
#define BLOCK_MSG_RUECKBLOCK			0x2B
#define BLOCK_MSG_ERLAUBNIS_ABGABE		0x2C
#define BLOCK_MSG_ERLAUBNIS_ANFRAGE		0x2D

#define BLOCK_MSG_VORBLOCK_ACK			0x8E
#define BLOCK_MSG_RUECKBLOCK_ACK		0x8F
#define BLOCK_MSG_ERLAUBNIS_ABGABE_ACK	0x90
#define BLOCK_MSG_ERLAUBNIS_ANFRAGE_ACK	0x91

#define BLOCK_MSG_DISTANT_SIGNAL		0x2F

#define BLOCK_MSG_BROADCAST				0x37

#define BLOCK_MSG_TRAIN_NUMBER			0x48
