nh-finescale/ln2block/src/HardwareTestLN2B/BlockPlatineTest/compile_options.h

#pragma once

//##########################################################################
//#
//#		compile_options.h
//#
//#	Hier werden Optionen für die Code Erzeugung definiert.
//#		-	DEBUGGING_PRINTOUT
//#			Wenn definiert, dann werden Informationen auf einem
//#			OLED-Display ausgegeben.
//#
//#		-	PLATINE_VERSION
//#			gibt an, für welche Platinen Version die Software
//#			kompiliert wird (Unterschiede in der I/O Belegung).
//#
//##########################################################################


//==========================================================================
//
//		C O D E   S E L E C T I O N   D E F I N I T I O N S
//
//==========================================================================

#define DEBUGGING_PRINTOUT

#define PLATINE_VERSION			5
